asinghani/drive-by-wireless/experimental/pwm/Servo/pwm_servo.c

#include "pico/stdlib.h"
#include <stdio.h>
#include "hardware/pwm.h"
#include "hardware/clocks.h"

float clockDiv = 64;
float wrap = 39062;

void setMillis(int servoPin, float millis)
{
    pwm_set_gpio_level(servoPin, (millis/20000.f)*wrap);
}

void setServo(int servoPin, float startMillis)
{
    gpio_set_function(servoPin, GPIO_FUNC_PWM);
    uint slice_num = pwm_gpio_to_slice_num(servoPin);

    pwm_config config = pwm_get_default_config();
    
    uint64_t clockspeed = clock_get_hz(5);
    clockDiv = 64;
    wrap = 39062;

    while (clockspeed/clockDiv/50 > 65535 && clockDiv < 256) clockDiv += 64; 
    wrap = clockspeed/clockDiv/50;

    pwm_config_set_clkdiv(&config, clockDiv);
    pwm_config_set_wrap(&config, wrap);

    pwm_init(slice_num, &config, true);

    setMillis(servoPin, startMillis);
}

bool direction = true;
int currentMillis = 1385;       //gives centre point (actual angle is 90deg from left wheel)
int servoPin = 22;

int main()
{
    setServo(servoPin, currentMillis);
    while (true)
    {
        currentMillis += (direction)?5:-5;
        if (currentMillis >= 1685) direction = false;   //Right MAX from vehicles point of view
        if (currentMillis <= 1085) direction = true;    //Left MAX from vehicles point of view
        if (currentMillis <= 1085) direction = true;
        setMillis(servoPin, currentMillis);
        sleep_ms(10);
    }
}
