asinghani/drive-by-wireless/experimental/uwb_unit_test/deca_device.c

/*! ------------------------------------------------------------------------------------------------------------------
 * @file    deca_device.c
 * @brief   Decawave device configuration and control functions
 *
 * @attention
 *
 * Copyright 2013-2020 (c) Decawave Ltd, Dublin, Ireland.
 * Copyright 2021 (c) Callender-Consulting, LLC
 *
 * All rights reserved.
 *
 */

#include <assert.h>
#include <stdlib.h>
#include <stdint.h>
#include <stdio.h>
#include <string.h>

#include "deca_types.h"
#include "deca_regs.h"
#include "deca_device_api.h"
#include "deca_version.h"
#include "uwb_config.h"

#include "pico/stdlib.h"
#include "pico/binary_info.h"
#include "hardware/spi.h"

// -------------------------------------------------------------------------------------------------------------------
// Module Macro definitions and enumerations
//

#if 0
  #define DWT_API_ERROR_CHECK  /* API checks config input parameters */
#endif

/* STS Minimum Threshold (STS_MNTH) needs to be adjusted with changing STS length.
To adjust the STS_MNTH following formula can be used: STS_MNTH = SQRT(X/Y)*default_STS_MNTH
default_STS_MNTH is 0x10
X is the length of the STS in units of 8 (i.e. 8 for 64 length, 16 for 128 length etc.)
Y is either 8 or 16, 8 when no PDOA or PDOA mode 1 and 16 for PDOA mode 3

The API does not use the formula and the STS_MNTH value is derived from approximation formula as given by get_sts_mnth()
function. The API here supports STS lengths as listed in: dwt_sts_lengths_e enum, which are: 32, 64, 128, 256, 512, 1024, 2048
The enum value is used as the index into sts_length_factors array. The array has values which are generated by:
val = SQRT(stsLength/16)*2048
*/
const uint16_t sts_length_factors[STS_LEN_SUPPORTED]=
{
    1024,1448,2048,2896,4096,5793,8192
};

static uint16_t get_sts_mnth(uint16_t sts, uint8_t default_threshold, uint8_t shift_val);

//DW-IC SPI CRC-8 polynomial
#define POLYNOMIAL  0x07    /* x^8 + x^2 + x^1 + x^0 */
#define TOPBIT      (1 << (8 - 1))

// OTP addresses definitions
#define LDOTUNELO_ADDRESS (0x04)
#define LDOTUNEHI_ADDRESS (0x05)
#define PARTID_ADDRESS  (0x06)
#define LOTID_ADDRESS   (0x07)
#define VBAT_ADDRESS    (0x08)
#define VTEMP_ADDRESS   (0x09)
#define XTRIM_ADDRESS   (0x1E)
#define OTPREV_ADDRESS  (0x1F)
#define BIAS_TUNE_ADDRESS (0xA)
#define DGC_TUNE_ADDRESS (0x20)

// dwt_readcarrierintegrator defines
#define B20_SIGN_EXTEND_TEST (0x00100000UL)
#define B20_SIGN_EXTEND_MASK (0xFFF00000UL)
#define DRX_CARRIER_INT_LEN  (3)

#define CIA_MANUALLOWERBOUND_TH_64  (0x10) //cia lower bound threshold values for 64 MHz PRF
#define STSQUAL_THRESH_64 (0.90f)
 //STS quality threshold values for 64 MHz PRF
 //when using 64 MHz PRF the stsCpQual should be > 90 % of STS length

// dwt_readclockoffset defines
#define B11_SIGN_EXTEND_TEST (0x1000UL)
#define B11_SIGN_EXTEND_MASK (0xE000UL)

// dwt_readpdoa defines
#define B12_SIGN_EXTEND_TEST (0x2000UL)
#define B12_SIGN_EXTEND_MASK (0xC000UL)

// -------------------------------------------------------------------------------------------------------------------
// Macros and Enumerations for SPI & CLock blocks
//
#define DW3000_SPI_FAC      (0<<6 | 1<<0)
#define DW3000_SPI_FARW     (0<<6 | 0<<0)
#define DW3000_SPI_EAMRW    (1<<6)

// Defines for enable_clocks function
#define FORCE_CLK_SYS_TX        (1)
#define FORCE_CLK_AUTO          (5)
//SYSCLK
#define FORCE_SYSCLK_PLL        (2)
#define FORCE_SYSCLK_FOSCDIV4   (1)
#define FORCE_SYSCLK_FOSC       (3)
//RX and TX CLK
#define FORCE_CLK_PLL           (2)

#define SEL_CHANNEL5            (5)
#define SEL_CHANNEL9            (9)

// -------------------------------------------------------------------------------------------------------------------
// Internal functions prototypes for controlling and configuring the device
//
static void dwt_force_clocks(int clocks);
static uint32_t _dwt_otpread(uint16_t address);                     // Read non-volatile memory
static void _dwt_otpprogword32(uint32_t data, uint16_t address);  // Program the non-volatile memory

// -------------------------------------------------------------------------------------------------------------------
// Data for DW3000 Decawave Transceiver control
//
// Structure to hold the device data
typedef struct
{
    uint32_t      partID ;            // IC Part ID - read during initialisation
    uint32_t      lotID ;             // IC Lot ID - read during initialisation
    uint8_t       bias_tune;          // bias tune code
    uint8_t       dgc_otp_set;        // Flag to check if DGC values are programmed in OTP
    uint8_t       vBatP;              // IC V bat read during production and stored in OTP (Vmeas @ 3V3)
    uint8_t       tempP;              // IC temp read during production and stored in OTP (Tmeas @ 23C)
    uint8_t       longFrames ;        // Flag in non-standard long frame mode
    uint8_t       otprev ;            // OTP revision number (read during initialisation)
    uint8_t       init_xtrim;         // initial XTAL trim value read from OTP (or defaulted to mid-range if OTP not programmed)
    uint8_t       dblbuffon;          // Double RX buffer mode and DB status flag
    uint16_t      sleep_mode;         // Used for automatic reloading of LDO tune and microcode at wake-up
    int16_t       ststhreshold;       // Threshold for deciding if received STS is good or bad
    dwt_spi_crc_mode_e   spicrc;      // Use SPI CRC when this flag is true
    uint8_t       stsconfig;          // STS configuration mode
    uint8_t       cia_diagnostic;     // CIA dignostic logging level
    dwt_cb_data_t cbData;             // Callback data structure
    dwt_spierrcb_t cbSPIRDErr;        // Callback for SPI read error events
    dwt_cb_t    cbTxDone;             // Callback for TX confirmation event
    dwt_cb_t    cbRxOk;               // Callback for RX good frame event
    dwt_cb_t    cbRxTo;               // Callback for RX timeout events
    dwt_cb_t    cbRxErr;              // Callback for RX error events
    dwt_cb_t    cbSPIErr;             // Callback for SPI error events
    dwt_cb_t    cbSPIRdy;             // Callback for SPI ready events
} dwt_local_data_t ;


// -------------------------------------------------------------------------------------------------------------------
// Local variables
//
static dwt_local_data_t   DW3000local[DWT_NUM_DW_DEV] ; // Local device data, can be an array to support multiple DW3000 testing applications/platforms
static dwt_local_data_t *pdw3000local = &DW3000local[0];   // Local data structure pointer
static uint8_t crcTable[256];

/*! ------------------------------------------------------------------------------------------------------------------
 * @brief This function returns the version of the API as defined by DW3000_DRIVER_VERSION
 *
 * input parameters
 *
 * output parameters
 *
 * returns version (DW3000_DRIVER_VERSION)
 */
int32_t dwt_apiversion(void)
{
    return DW3000_DRIVER_VERSION;
}

/*! ------------------------------------------------------------------------------------------------------------------
 * @brief This function sets the local data structure pointer to point to the element in the local array as given by the index.
 *
 * input parameters
 * @param index    - selects the array element to point to. Must be within the array bounds, i.e. < DWT_NUM_DW_DEV
 *
 * output parameters
 *
 * returns DWT_SUCCESS for success, or DWT_ERROR for error
 */
int dwt_setlocaldataptr(unsigned int index)
{
    // Check the index is within the array bounds
    if (DWT_NUM_DW_DEV <= index) // return error if index outside the array bounds
    {
        return DWT_ERROR ;
    }

    pdw3000local = &DW3000local[index];

    return DWT_SUCCESS ;
}

/*! ------------------------------------------------------------------------------------------------------------------
* @brief  this function is used to read/write to the DW3000 device registers
*
* input parameters:
* @param recordNumber  - ID of register file or buffer being accessed
* @param index         - byte index into register file or buffer being accessed
* @param length        - number of bytes being written
* @param buffer        - pointer to buffer containing the 'length' bytes to be written
* @param rw            - DW3000_SPI_WR_BIT/DW3000_SPI_RD_BIT
*
* no return value
*/
static
void dwt_xfer3000
(
    const uint32_t    regFileID,  //0x0, 0x04-0x7F ; 0x10000, 0x10004, 0x10008-0x1007F; 0x20000 etc
    const uint16_t    indx,       //sub-index, calculated from regFileID 0..0x7F,
    const uint16_t    length,
    uint8_t           *buffer,
    const spi_modes_e mode
)
{
    uint8_t  header[2];           // Buffer to compose header in
    uint16_t cnt = 0;             // Counter for length of a header

    uint16_t reg_file     = 0x1F & ((regFileID + indx) >> 16);
    uint16_t reg_offset   = 0x7F &  (regFileID + indx);

    assert(reg_file     <= 0x1F);
    assert(reg_offset   <= 0x7F);
    assert(length       < 0x3100);
    assert(mode == DW3000_SPI_WR_BIT ||\
           mode == DW3000_SPI_RD_BIT ||\
           mode == DW3000_SPI_AND_OR_8 ||\
           mode == DW3000_SPI_AND_OR_16 ||\
           mode == DW3000_SPI_AND_OR_32);

    // Write message header selecting WRITE operation and addresses as appropriate
    uint16_t  addr;
    addr = (reg_file << 9) | (reg_offset << 2);

    header[0] = (uint8_t)((mode | addr) >> 8);//  & 0xFF; //bit7 + addr[4:0] + sub_addr[6:6]
    header[1] = (uint8_t)(addr | (mode & 0x03));// & 0xFF; //EAM: subaddr[5:0]+ R/W/AND_OR

    if (/*reg_offset == 0 && */length == 0)
    {   /* Fast Access Commands (FAC)
         * only write operation is possible for this mode
         * bit_7=one is W operation, bit_6=zero: FastAccess command, bit_[5..1] addr, bits_0=one: MODE of FastAccess
         */
        assert(mode == DW3000_SPI_WR_BIT);

        header[0] = (uint8_t)((DW3000_SPI_WR_BIT>>8) | (regFileID<<1) | DW3000_SPI_FAC);
        cnt = 1;
    }
    else if (reg_offset == 0 /*&& length > 0*/ && (mode == DW3000_SPI_WR_BIT || mode == DW3000_SPI_RD_BIT))
    {   /* Fast Access Commands with Read/Write support (FACRW)
         * bit_7 is R/W operation, bit_6=zero: FastAccess command, bit_[5..1] addr, bits_0=zero: MODE of FastAccess
         */
        header[0] |= DW3000_SPI_FARW;
        cnt = 1;
    }
    else
    {   /* Extended Address Mode with Read/Write support (EAMRW)
         * b[0] = bit_7 is R/W operation, bit_6 one = ExtendedAddressMode;
         * b[1] = addr<<2 | (mode&0x3)
         */
        header[0] |= DW3000_SPI_EAMRW;
        cnt = 2;
    }

    switch (mode)
    {
    case    DW3000_SPI_AND_OR_8:
    case    DW3000_SPI_AND_OR_16:
    case    DW3000_SPI_AND_OR_32:
    case    DW3000_SPI_WR_BIT:
    {
        uint8_t crc8 = 0;
        if (pdw3000local->spicrc != DWT_SPI_CRC_MODE_NO)
        {
            //generate 8 bit CRC
            crc8 = dwt_generatecrc8(header, cnt, 0);
            crc8 = dwt_generatecrc8(buffer, length, crc8);

            // Write it to the SPI
            writetospiwithcrc(cnt, header, length, buffer, crc8);
        }
        else
        {
            // Write it to the SPI
            writetospi(cnt, header, length, buffer);
        }
        break;
    }
    case DW3000_SPI_RD_BIT:
        {
            readfromspi(cnt, header, length, buffer);

            //check that the SPI read has correct CRC-8 byte
            //also don't do for SPICRC_CFG_ID register itself to prevent infinite recursion
            if ((pdw3000local->spicrc == DWT_SPI_CRC_MODE_WRRD) && (regFileID != SPICRC_CFG_ID))
            {
                uint8_t crc8, dwcrc8;
                //generate 8 bit CRC from the read data
                crc8 = dwt_generatecrc8(header, cnt, 0);
                crc8 = dwt_generatecrc8(buffer, length, crc8);

                //read the CRC that was generated in the DW3000 for the read transaction
                dwcrc8 = dwt_read8bitoffsetreg(SPICRC_CFG_ID, 0);

                //if the two CRC don't match report SPI read error
                //potential problem in callback if it will try to read/write SPI with CRC again.
                if (crc8 != dwcrc8)
                {
                    if (pdw3000local->cbSPIRDErr != NULL)
                        pdw3000local->cbSPIRDErr();
                }

            }
            break;
        }
    default:
        while(1);
        break;
    }

} // end dwt_xfer3000()

/*! ------------------------------------------------------------------------------------------------------------------
 * @brief  this function is used to write to the DW3000 device registers
 *
 * input parameters:
 * @param recordNumber  - ID of register file or buffer being accessed
 * @param index         - byte index into register file or buffer being accessed
 * @param length        - number of bytes being written
 * @param buffer        - pointer to buffer containing the 'length' bytes to be written
 *
 * output parameters
 *
 * no return value
 */
//static
void dwt_writetodevice
(
    uint32_t      regFileID,
    uint16_t      index,
    uint16_t      length,
    uint8_t       *buffer
)
{
    dwt_xfer3000(regFileID, index, length, buffer, DW3000_SPI_WR_BIT);
}

/*! ------------------------------------------------------------------------------------------------------------------
 * @brief  This function wakeup device by an IO pin. DW3000 SPI_CS or WAKEUP pins can be used for this.
 *         wakeup_device_with_io() which is external to this file and is platform dependant and it should be modified to
 *         toggle the correct pin depending on the HW/MCU connections with DW3000.
 *
 * @param None
 *
 * output parameters
 *
 * no return value
 */
void dwt_wakeup_ic(void)
{
    wakeup_device_with_io();
}

/*! ------------------------------------------------------------------------------------------------------------------
 * @brief  this function is used to read from the DW3000 device registers
 *
 * @param recordNumber  - ID of register file or buffer being accessed
 * @param index         - byte index into register file or buffer being accessed
 * @param length        - number of bytes being read
 * @param buffer        - pointer to buffer in which to return the read data.
 *
 * output parameters
 *
 * no return value
 */
//static
void dwt_readfromdevice
(
    uint32_t  regFileID,
    uint16_t  index,
    uint16_t  length,
    uint8_t   *buffer
)
{
    dwt_xfer3000(regFileID, index, length, buffer, DW3000_SPI_RD_BIT);
}

/*! ------------------------------------------------------------------------------------------------------------------
 * @brief  this function is used to read 32-bit value from the DW3000 device registers
 *
 * input parameters:
 * @param regFileID - ID of register file or buffer being accessed
 * @param regOffset - the index into register file or buffer being accessed
 *
 * output parameters
 *
 * returns 32 bit register value
 */
uint32_t dwt_read32bitoffsetreg(int regFileID, int regOffset)
{
    int     j ;
    uint32_t  regval = 0 ;
    uint8_t   buffer[4] ;

    dwt_readfromdevice(regFileID,regOffset,4,buffer); // Read 4 bytes (32-bits) register into buffer

    for (j = 3 ; j >= 0 ; j --)
    {
        regval = (regval << 8) + buffer[j] ;
    }

    return (regval);

} // end dwt_read32bitoffsetreg()

/*! ------------------------------------------------------------------------------------------------------------------
 * @brief  this function is used to read 16-bit value from the DW3000 device registers
 *
 * input parameters:
 * @param regFileID - ID of register file or buffer being accessed
 * @param regOffset - the index into register file or buffer being accessed
 *
 * output parameters
 *
 * returns 16 bit register value
 */
uint16_t dwt_read16bitoffsetreg(int regFileID,int regOffset)
{
    uint16_t  regval = 0 ;
    uint8_t   buffer[2] ;

    dwt_readfromdevice(regFileID,regOffset,2,buffer); // Read 2 bytes (16-bits) register into buffer

    regval = ((uint16_t)buffer[1] << 8) + buffer[0] ;
    return regval ;

} // end dwt_read16bitoffsetreg()

/*! ------------------------------------------------------------------------------------------------------------------
 * @brief  this function is used to read an 8-bit value from the DW3000 device registers
 *
 * input parameters:
 * @param regFileID - ID of register file or buffer being accessed
 * @param regOffset - the index into register file or buffer being accessed
 *
 * output parameters
 *
 * returns 8-bit register value
 */
uint8_t dwt_read8bitoffsetreg(int regFileID, int regOffset)
{
    uint8_t regval;

    dwt_readfromdevice(regFileID, regOffset, 1, &regval);

    return regval ;
}

/*! ------------------------------------------------------------------------------------------------------------------
 * @brief  this function is used to write 32-bit value to the DW3000 device registers
 *
 * input parameters:
 * @param regFileID - ID of register file or buffer being accessed
 * @param regOffset - the index into register file or buffer being accessed
 * @param regval    - the value to write
 *
 * output parameters
 *
 * no return value
 */
void dwt_write32bitoffsetreg(int regFileID, int regOffset, uint32_t regval)
{
    int     j ;
    uint8_t   buffer[4] ;

    for ( j = 0 ; j < 4 ; j++ )
    {
        buffer[j] = (uint8_t)regval;
        regval >>= 8 ;
    }

    dwt_writetodevice(regFileID,regOffset,4,buffer);
} // end dwt_write32bitoffsetreg()

/*! ------------------------------------------------------------------------------------------------------------------
 * @brief  this function is used to write 16-bit value to the DW3000 device registers
 *
 * input parameters:
 * @param regFileID - ID of register file or buffer being accessed
 * @param regOffset - the index into register file or buffer being accessed
 * @param regval    - the value to write
 *
 * output parameters
 *
 * no return value
 */
void dwt_write16bitoffsetreg(int regFileID, int regOffset, uint16_t regval)
{
    uint8_t   buffer[2] ;

    buffer[0] = (uint8_t)regval;
    buffer[1] = regval >> 8 ;

    dwt_writetodevice(regFileID,regOffset,2,buffer);
} // end dwt_write16bitoffsetreg()

/*! ------------------------------------------------------------------------------------------------------------------
 * @brief  this function is used to write an 8-bit value to the DW3000 device registers
 *
 * input parameters:
 * @param regFileID - ID of register file or buffer being accessed
 * @param regOffset - the index into register file or buffer being accessed
 * @param regval    - the value to write
 *
 * output parameters
 *
 * no return value
 */
void dwt_write8bitoffsetreg(int regFileID, int regOffset, uint8_t regval)
{
    //uint8_t   buf[1];
    //buf[0] = regval;
    dwt_writetodevice(regFileID, regOffset, 1, &regval);
}

/*! ------------------------------------------------------------------------------------------------------------------
 * @brief  this function is used to modify a 32-bit value to the DW3000 device registers
 *
 * input parameters:
 * @param regFileID :   ID of register file or buffer being accessed
 * @param regOffset :   the index into register file or buffer being accessed
 * @param regval_and:   the value to AND to register
 * @param regval_or :   the value to OR to register
 * @output          :   no return value
 */
void dwt_modify32bitoffsetreg(const int regFileID, const int regOffset, const uint32_t _and, const uint32_t _or)
{
    uint8_t buf[8];
    buf[0] = (uint8_t)_and;//       &0xFF;
    buf[1] = (uint8_t)(_and>>8);//  &0xFF;
    buf[2] = (uint8_t)(_and>>16);// &0xFF;
    buf[3] = (uint8_t)(_and>>24);// &0xFF;
    buf[4] = (uint8_t)_or;//        &0xFF;
    buf[5] = (uint8_t)(_or>>8);//   &0xFF;
    buf[6] = (uint8_t)(_or>>16);//  &0xFF;
    buf[7] = (uint8_t)(_or>>24);//  &0xFF;
    dwt_xfer3000(regFileID, regOffset, sizeof(buf), buf, DW3000_SPI_AND_OR_32);
}

/*! ------------------------------------------------------------------------------------------------------------------
 * @brief  this function is used to modify a 16-bit value to the DW3000 device registers
 *
 * input parameters:
 * @param regFileID :   ID of register file or buffer being accessed
 * @param regOffset :   the index into register file or buffer being accessed
 * @param regval_and:   the value to AND to register
 * @param regval_or :   the value to OR to register
 * @output          :   no return value
 */
void dwt_modify16bitoffsetreg(const int regFileID, const int regOffset, const uint16_t _and, const uint16_t _or)
{
    uint8_t buf[4];
    buf[0] = (uint8_t)_and;//       &0xFF;
    buf[1] = (uint8_t)(_and>>8);//  &0xFF;
    buf[2] = (uint8_t)_or;//        &0xFF;
    buf[3] = (uint8_t)(_or>>8);//   &0xFF;
    dwt_xfer3000(regFileID, regOffset, sizeof(buf), buf, DW3000_SPI_AND_OR_16);
}

/*! ------------------------------------------------------------------------------------------------------------------
 * @brief  this function is used to modify a 8-bit value to the DW3000 device registers
 *
 * input parameters:
 * @param regFileID :   ID of register file or buffer being accessed
 * @param regOffset :   the index into register file or buffer being accessed
 * @param regval_and:   the value to AND to register
 * @param regval_or :   the value to OR to register
 * @output          :   no return value
 */
void dwt_modify8bitoffsetreg(const int regFileID, const int regOffset, const uint8_t _and, const uint8_t _or)
{
    uint8_t buf[2];
    buf[0] = _and;
    buf[1] = _or;
    dwt_xfer3000(regFileID, regOffset, sizeof(buf),buf, DW3000_SPI_AND_OR_8);
}

static
void _dwt_crc8init(void)
{
    uint8_t  remainder;
    int dividend;

    /*
    * Compute the remainder of each possible dividend.
    */
    for (dividend = 0; dividend < 256; ++dividend)
    {
        /*
        * Start with the dividend followed by zeros.
        */
        remainder = dividend;

        /*
        * Perform modulo-2 division, a bit at a time.
        */
        for (uint8_t bit = 8; bit > 0; --bit)
        {
            /*
            * Try to divide the current data bit.
            */
            if (remainder & TOPBIT)
            {
                remainder = (remainder << 1) ^ POLYNOMIAL;
            }
            else
            {
                remainder = (remainder << 1);
            }
        }

        /*
        * Store the result into the table.
        */
        crcTable[dividend] = remainder;
    }

}   /* _dwt_crc8init() */

/*! ------------------------------------------------------------------------------------------------------------------
* @brief  this function is used to calculate 8-bit CRC, it uses 100000111 polynomial (i.e. P(x) = x^8+ x^2+ x^1+ x^0)
* this function has been optimized to use crcTable[] and calculate the CRC on byte by byte basis.
*
* input parameters:
* @param byteArray         - data to calculate CRC for
* @param len               - length of byteArray
* @param crcRemainderInit  - the remainder is the crc, also it is initially set to the initialisation value for CRC calculation
*
* output parameters
*
* returns 8-bit calculate CRC value
*/
uint8_t dwt_generatecrc8(const uint8_t* byteArray, int len, uint8_t crcRemainderInit)
{
    uint8_t data;
    int byte;

    /*
    * Divide the message by the polynomial, a byte at a time.
    */
    for (byte = 0; byte < len; ++byte)
    {
        data = byteArray[byte] ^ crcRemainderInit;
        crcRemainderInit = crcTable[data];// ^ (crcRemainderInit << 8);
    }

    /*
    * The final remainder is the CRC.
    */
    return(crcRemainderInit);
}

/*! ------------------------------------------------------------------------------------------------------------------
* @brief This is used to enable SPI CRC check in DW3000
*
* input parameters
* @param crc_mode - if set to DWT_SPI_CRC_MODE_WR then SPI CRC checking will be performed in DW3000 on each SPI write
*                   last byte of the SPI write transaction needs to be the 8-bit CRC, if it does not match
*                   the one calculated by DW3000 SPI CRC ERROR event will be set in the status register (SYS_STATUS_SPICRC)
*
* @param spireaderr_cb - this needs to contain the callback function pointer which will be called when SPI read error
*                        is detected (when the DW3000 generated CRC does not match the one calculated by  dwt_generatecrc8
*                        following the SPI read transaction)
*
* output parameters
*
* no return value
*/
void dwt_enablespicrccheck(dwt_spi_crc_mode_e crc_mode, dwt_spierrcb_t spireaderr_cb)
{
    if (crc_mode != DWT_SPI_CRC_MODE_NO) //enable CRC check in DW3000
    {
        dwt_or8bitoffsetreg(SYS_CFG_ID, 0, SYS_CFG_SPI_CRC_BIT_MASK);

        if (crc_mode == DWT_SPI_CRC_MODE_WRRD) //enable CRC generation on SPI read transaction which the DW3000 will store in SPICRC_CFG_ID register
        {
            pdw3000local->cbSPIRDErr = spireaderr_cb;
        }
        //initialise the crc calculation lookup table
        _dwt_crc8init();
    }
    else
    {
        dwt_and8bitoffsetreg(SYS_CFG_ID, 0, (uint8_t)~SYS_CFG_SPI_CRC_BIT_MASK);
    }
    pdw3000local->spicrc = crc_mode;
}

static
void _dwt_prog_ldo_and_bias_tune(void)
{
    dwt_or16bitoffsetreg(OTP_CFG_ID, 0, LDO_BIAS_KICK);
    dwt_and_or16bitoffsetreg(BIAS_CTRL_ID, 0, (uint16_t)~BIAS_CTRL_BIAS_MASK, pdw3000local->bias_tune);
}

/*! ------------------------------------------------------------------------------------------------------------------
* @brief This function is a static function used to 'kick' the desired operating parameter set (OPS) table upon wakeup from sleep.
*        It will load the required OPS table configuration based upon what OPS table was set to be used in dwt_configure().
*
* input parameters
*
* output parameters
*
* no return value
*/
static
void _dwt_kick_ops_table_on_wakeup(void)
{
    /* Restore OPS table config and kick. */
    /* Correct sleep mode should be set by dwt_configure() */

    /* Using the mask of all available OPS table options, check for OPS table options in the sleep mode mask */
    switch (pdw3000local->sleep_mode & (DWT_ALT_OPS | DWT_SEL_OPS0 | DWT_SEL_OPS1 | DWT_SEL_OPS2 | DWT_SEL_OPS3))
    {
    /* If preamble length >= 256 and set by dwt_configure(), the OPS table should be kicked off like so upon wakeup. */
    case (DWT_ALT_OPS | DWT_SEL_OPS0):
        dwt_modify32bitoffsetreg(OTP_CFG_ID, 0, ~(OTP_CFG_OPS_ID_BIT_MASK), DWT_OPSET_LONG | OTP_CFG_OPS_KICK_BIT_MASK);
        break;
    /* If SCP mode is enabled by dwt_configure(), the OPS table should be kicked off like so upon wakeup. */
    case (DWT_ALT_OPS | DWT_SEL_OPS1):
        dwt_modify32bitoffsetreg(OTP_CFG_ID, 0, ~(OTP_CFG_OPS_ID_BIT_MASK), DWT_OPSET_SCP | OTP_CFG_OPS_KICK_BIT_MASK);
        break;
    default:
        break;
    }
}

/*! ------------------------------------------------------------------------------------------------------------------
* @brief This function is a static function used to 'kick' the DGC upon wakeup from sleep. It will load the
*        required DGC configuration from OTP based upon what channel was set to be used in dwt_configure().
*
* input parameters
* @param channel - specifies the operating channel (e.g. 5 or 9)
*
* output parameters
*
* no return value
*/
static
void _dwt_kick_dgc_on_wakeup(int8_t channel)
{
    /* The DGC_SEL bit must be set to '0' for channel 5 and '1' for channel 9 */
    if (channel == 5)
    {
        dwt_modify32bitoffsetreg(OTP_CFG_ID, 0, ~(OTP_CFG_DGC_SEL_BIT_MASK),
                (DWT_DGC_SEL_CH5 << OTP_CFG_DGC_SEL_BIT_OFFSET) | OTP_CFG_DGC_KICK_BIT_MASK);
    }
    else if (channel == 9)
    {
        dwt_modify32bitoffsetreg(OTP_CFG_ID, 0, ~(OTP_CFG_DGC_SEL_BIT_MASK),
                (DWT_DGC_SEL_CH9 << OTP_CFG_DGC_SEL_BIT_OFFSET) | OTP_CFG_DGC_KICK_BIT_MASK);
    }
}

/*! ------------------------------------------------------------------------------------------------------------------
 * @brief This function initialises the DW3000 transceiver:
 * it reads its DEV_ID register (address 0x00) to verify the IC is one supported
 * by this software (e.g. DW3000 32-bit device ID value is 0xDECA03xx).  Then it
 * does any initial once only device configurations needed for use and initialises
 * as necessary any static data items belonging to this low-level driver.
 *
 * NOTES:
 * 1.it also reads and applies LDO and BIAS tune and crystal trim values from OTP memory
 * 2.it is assumed this function is called after a reset or on power up of the DW3000
 *
 * input parameters
 * @param mode - mask which defines which OTP values to read.
 *
 * output parameters
 *
 * returns DWT_SUCCESS for success, or DWT_ERROR for error
 */
int dwt_initialise(int mode)
{
   //uint16_t otp_addr;
   //uint32_t devid;
    uint32_t ldo_tune_lo;
    uint32_t ldo_tune_hi;

    pdw3000local->dblbuffon = DBL_BUFF_OFF; // Double buffer mode off by default / clear the flag
    pdw3000local->sleep_mode = DWT_RUNSAR;  // Configure RUN_SAR on wake by default as it is needed when running PGF_CAL
    pdw3000local->spicrc = 0;
    pdw3000local->stsconfig = 0; //STS off
    pdw3000local->vBatP = 0;
    pdw3000local->tempP = 0;

    pdw3000local->cbTxDone = NULL;
    pdw3000local->cbRxOk = NULL;
    pdw3000local->cbRxTo = NULL;
    pdw3000local->cbRxErr = NULL;
    pdw3000local->cbSPIRdy = NULL;
    pdw3000local->cbSPIErr = NULL;

    // Read and validate device ID return -1 if not recognised
    if (dwt_check_dev_id()!=DWT_SUCCESS)
    {
        return DWT_ERROR;
    }

    //Read LDO_TUNE and BIAS_TUNE from OTP
    ldo_tune_lo = _dwt_otpread(LDOTUNELO_ADDRESS);
    ldo_tune_hi = _dwt_otpread(LDOTUNEHI_ADDRESS);
    pdw3000local->bias_tune = (_dwt_otpread(BIAS_TUNE_ADDRESS) >> 16) & BIAS_CTRL_BIAS_MASK;

    if ((ldo_tune_lo != 0) && (ldo_tune_hi != 0) && (pdw3000local->bias_tune != 0))
    {
        _dwt_prog_ldo_and_bias_tune();
    }

    // Read DGC_CFG from OTP
    if (_dwt_otpread(DGC_TUNE_ADDRESS) == DWT_DGC_CFG0)
    {
        pdw3000local->dgc_otp_set = DWT_DGC_LOAD_FROM_OTP;
    }
    else
    {
        pdw3000local->dgc_otp_set = DWT_DGC_LOAD_FROM_SW;
    }

    // Load Part and Lot ID from OTP
    if(mode & DWT_READ_OTP_PID)
        pdw3000local->partID = _dwt_otpread(PARTID_ADDRESS);
    if (mode & DWT_READ_OTP_LID)
        pdw3000local->lotID = _dwt_otpread(LOTID_ADDRESS);
    if (mode & DWT_READ_OTP_BAT)
        pdw3000local->vBatP = (uint8_t)_dwt_otpread(VBAT_ADDRESS);
    if (mode & DWT_READ_OTP_TMP)
        pdw3000local->tempP = (uint8_t)_dwt_otpread(VTEMP_ADDRESS);


    if(pdw3000local->tempP == 0) //if the reference temperature has not been programmed in OTP (early eng samples) set to default value
    {
        pdw3000local->tempP = 0x85 ; //@temp of 20 deg
    }

    if(pdw3000local->vBatP == 0) //if the reference voltage has not been programmed in OTP (early eng samples) set to default value
    {
        pdw3000local->vBatP = 0x74 ;  //@Vref of 3.0V
    }

    pdw3000local->otprev = (uint8_t) _dwt_otpread(OTPREV_ADDRESS);

    pdw3000local->init_xtrim = _dwt_otpread(XTRIM_ADDRESS) & 0x7f;
    if(pdw3000local->init_xtrim == 0)
    {
        pdw3000local->init_xtrim = 0x2E ; //set default value
    }
    dwt_write8bitoffsetreg(XTAL_ID, 0, pdw3000local->init_xtrim);


    return DWT_SUCCESS ;

} // end dwt_initialise()

/*! ------------------------------------------------------------------------------------------------------------------
 * @brief This function can place DW3000 into IDLE/IDLE_PLL or IDLE_RC mode when it is not actively in TX or RX.
 *
 * input parameters
 * @param state - DWT_DW_IDLE (1) to put DW3000 into IDLE/IDLE_PLL state; DWT_DW_INIT (0) to put DW3000 into INIT_RC state;
 *                DWT_DW_IDLE_RC (2) to put DW3000 into IDLE_RC state.
 *
 * output parameters none
 *
 * no return value
 */
void dwt_setdwstate(int state)
{
    if (state == DWT_DW_IDLE) // Set the auto INIT2IDLE bit so that DW3000 enters IDLE mode before switching clocks to system_PLL
    //NOTE: PLL should be configured prior to this, and the device should be in IDLE_RC (if the PLL does not lock device will remain in IDLE_RC)
    {
        //switch clock to auto - if coming here from INIT_RC the clock will be FOSC/4, need to switch to auto prior to setting auto INIT2IDLE bit
        dwt_force_clocks(FORCE_CLK_AUTO);
        dwt_or8bitoffsetreg(SEQ_CTRL_ID, 0x01, SEQ_CTRL_AINIT2IDLE_BIT_MASK>>8);
    }
    else if(state == DWT_DW_IDLE_RC)  //Change state to IDLE_RC and clear auto INIT2IDLE bit
    {
        //switch clock to FOSC
        dwt_or8bitoffsetreg(CLK_CTRL_ID, 0, FORCE_SYSCLK_FOSC);
        //clear the auto INIT2IDLE bit and set FORCE2INIT
        dwt_modify32bitoffsetreg(SEQ_CTRL_ID, 0x0, (uint32_t) ~SEQ_CTRL_AINIT2IDLE_BIT_MASK, SEQ_CTRL_FORCE2INIT_BIT_MASK);
        //clear force bits (device will stay in IDLE_RC)
        dwt_and8bitoffsetreg(SEQ_CTRL_ID, 0x2, (uint8_t) ~(SEQ_CTRL_FORCE2INIT_BIT_MASK>>16));
        //switch clock to auto
        dwt_force_clocks(FORCE_CLK_AUTO);
    }
    else
    //NOTE: the SPI rate needs to be <= 7MHz as device is switching to INIT_RC state
    {
        dwt_or8bitoffsetreg(CLK_CTRL_ID, 0, FORCE_SYSCLK_FOSCDIV4);
        //clear the auto INIT2IDLE bit and set FORCE2INIT
        dwt_modify32bitoffsetreg(SEQ_CTRL_ID, 0x0, (uint32_t) ~SEQ_CTRL_AINIT2IDLE_BIT_MASK, SEQ_CTRL_FORCE2INIT_BIT_MASK);
        dwt_and8bitoffsetreg(SEQ_CTRL_ID, 0x2, (uint8_t) ~(SEQ_CTRL_FORCE2INIT_BIT_MASK>>16));
    }
}

/*! ------------------------------------------------------------------------------------------------------------------
 * @brief This is used to enable GPIO clocks. The clocks are needed to ensure correct GPIO operation
 *
 * input parameters
 *
 * output parameters
 *
 * no return value
 */
void dwt_enablegpioclocks(void)
{
    dwt_or32bitoffsetreg(CLK_CTRL_ID, 0, CLK_CTRL_GPIO_CLK_EN_BIT_MASK);
}

/*! ------------------------------------------------------------------------------------------------------------------
 * @brief This is used to return the read OTP revision
 *
 * NOTE: dwt_initialise() must be called prior to this function so that it can return a relevant value.
 *
 * input parameters
 *
 * output parameters
 *
 * returns the read OTP revision value
 */
uint8_t dwt_otprevision(void)
{
    return pdw3000local->otprev ;
}

/*! ------------------------------------------------------------------------------------------------------------------
 * @brief This function enables/disables the fine grain TX sequencing (this is enabled by default in the DW3000).
 *
 * input parameters
 * @param enable - 1 to enable fine grain TX sequencing, 0 to disable it.
 *
 * output parameters none
 *
 * no return value
 */
void dwt_setfinegraintxseq(int enable)
{
    if (enable)
    {
        dwt_write32bitoffsetreg(PWR_UP_TIMES_LO_ID, 2, PMSC_TXFINESEQ_ENABLE);
    }
    else
    {
        dwt_write32bitoffsetreg(PWR_UP_TIMES_LO_ID, 2, PMSC_TXFINESEQ_DISABLE);
    }
}

/*! ------------------------------------------------------------------------------------------------------------------
 * @brief This is used to enable GPIO for external LNA or PA functionality - HW dependent, consult the DW3000 User Manual.
 *        This can also be used for debug as enabling TX and RX GPIOs is quite handy to monitor DW3000's activity.
 *
 * NOTE: Enabling PA functionality requires that fine grain TX sequencing is deactivated. This can be done using
 *       dwt_setfinegraintxseq().
 *
 * input parameters
 * @param lna_pa - bit field: bit 0 if set will enable LNA functionality,
 *                          : bit 1 if set will enable PA functionality,
 *                          : to disable LNA/PA set the bits to 0
 * output parameters
 *
 * no return value
 */
void dwt_setlnapamode(int lna_pa)
{
    uint32_t gpio_mode = dwt_read32bitreg(GPIO_MODE_ID);
    gpio_mode &= (~(GPIO_MODE_MSGP0_MODE_BIT_MASK | GPIO_MODE_MSGP1_MODE_BIT_MASK
            | GPIO_MODE_MSGP4_MODE_BIT_MASK | GPIO_MODE_MSGP5_MODE_BIT_MASK | GPIO_MODE_MSGP6_MODE_BIT_MASK)); //clear GPIO 4, 5, 6, configuration
    if (lna_pa & DWT_LNA_ENABLE)
    {
        gpio_mode |= GPIO_PIN6_EXTRX;
    }
    if (lna_pa & DWT_PA_ENABLE)
    {
        gpio_mode |= (GPIO_PIN4_EXTDA | GPIO_PIN5_EXTTX);
    }
    if (lna_pa & DWT_TXRX_EN)
    {
        gpio_mode |= (GPIO_PIN0_EXTTXE | GPIO_PIN1_EXTRXE);
    }

    dwt_write32bitreg(GPIO_MODE_ID, gpio_mode);
}

/*! ------------------------------------------------------------------------------------------------------------------
 * @brief Returns the PG delay value of the TX
 *
 * input parameters
 *
 * output parameters
 *
 * returns uint8_t
 */
uint8_t dwt_readpgdelay(void)
{
    return dwt_read8bitoffsetreg(TX_CTRL_HI_ID, 0);
}

/*! ------------------------------------------------------------------------------------------------------------------
 * @brief This is used to return the read V measured @ 3.3 V value recorded in OTP address 0x8 (VBAT_ADDRESS)
 *
 * NOTE: dwt_initialise() must be called prior to this function so that it can return a relevant value.
 *
 * input parameters
 *
 * output parameters
 *
 * returns the 8 bit V bat value as programmed in the factory
 */
uint8_t dwt_geticrefvolt(void)
{
    return pdw3000local->vBatP;
}

/*! ------------------------------------------------------------------------------------------------------------------
* @brief This is used to return the read T measured @ 23 C value recorded in OTP address 0x9 (VTEMP_ADDRESS)
*
* NOTE: dwt_initialise() must be called prior to this function so that it can return a relevant value.
*
* input parameters
*
* output parameters
*
* returns the 8 bit V temp value as programmed in the factory
*/
uint8_t dwt_geticreftemp(void)
{
    return pdw3000local->tempP;
}

/*! ------------------------------------------------------------------------------------------------------------------
 * @brief This is used to return the read part ID of the device
 *
 * NOTE: dwt_initialise() must be called prior to this function so that it can return a relevant value.
 *
 * input parameters
 *
 * output parameters
 *
 * returns the 32 bit part ID value as programmed in the factory
 */
uint32_t dwt_getpartid(void)
{
    return pdw3000local->partID;
}

/*! ------------------------------------------------------------------------------------------------------------------
 * @brief This is used to return the read lot ID of the device
 *
 * NOTE: dwt_initialise() must be called prior to this function so that it can return a relevant value.
 *
 * input parameters
 *
 * output parameters
 *
 * returns the 32 bit lot ID value as programmed in the factory
 */
uint32_t dwt_getlotid(void)
{
    return pdw3000local->lotID;
}

/*! ------------------------------------------------------------------------------------------------------------------
 * @brief This is used to return the read device type and revision information of the DW3000 device (MP part is 0xDECA0300)
 *
 * input parameters
 *
 * output parameters
 *
 * returns the read value which for DW3000 is 0xDECA0312/0xDECA0302
 */
uint32_t dwt_readdevid(void)
{
    return dwt_read32bitoffsetreg(DEV_ID_ID, 0);
}

/*! ------------------------------------------------------------------------------------------------------------------
 * @brief This function provides the API for the configuration of the TX spectrum
 * including the power and pulse generator delay. The input is a pointer to the data structure
 * of type dwt_txconfig_t that holds all the configurable items.
 *
 * input parameters
 * @param config    -   pointer to the txrf configuration structure, which contains the tx rf config data
 *                      If config->PGcount == 0 the PGdelay value will be used, else the PG calibration will run
 *
 * output parameters
 *
 * no return value
 */
void dwt_configuretxrf(dwt_txconfig_t *config)
{
    if (config->PGcount == 0) {
        // Configure RF TX PG_DELAY
        dwt_write8bitoffsetreg(TX_CTRL_HI_ID, 0, config->PGdly);
    }
    else
    {
        uint8_t channel = 5;
        if (dwt_read8bitoffsetreg(CHAN_CTRL_ID, 0) & 0x1)
        {
            channel = 9;
        }
        dwt_calcbandwidthadj(config->PGcount, channel);
    }

    // Configure TX power
    dwt_write32bitreg(TX_POWER_ID, config->power);
}

/*! ------------------------------------------------------------------------------------------------------------------
 * @brief This function configures the STS AES 128 bit key value.
 * the default value is [31:00]c9a375fa,
 *                      [63:32]8df43a20,
 *                      [95:64]b5e5a4ed,
 *                     [127:96]0738123b
 *
 * input parameters
 * @param pStsKey - the pointer to the structure of dwt_sts_cp_key_t type, which holds the AES128 key value to generate STS
 *
 * output parameters
 *
 * no return value
 */
void dwt_configurestskey(dwt_sts_cp_key_t* pStsKey)
{
    dwt_write32bitreg(STS_KEY0_ID, pStsKey->key0);
    dwt_write32bitreg(STS_KEY1_ID, pStsKey->key1);
    dwt_write32bitreg(STS_KEY2_ID, pStsKey->key2);
    dwt_write32bitreg(STS_KEY3_ID, pStsKey->key3);
}

/*! ------------------------------------------------------------------------------------------------------------------
 * @brief This function configures the STS AES 128 bit initial value, the default value is 1, i.e. DW3000 reset value is 1.
 *
 * input parameters
 * @param pStsIv - the pointer to the structure of dwt_sts_cp_iv_t type, which holds the IV value to generate STS
 *
 * output parameters
 *
 * no return value
 */
void dwt_configurestsiv(dwt_sts_cp_iv_t* pStsIv)
{
    dwt_write32bitreg(STS_IV0_ID, pStsIv->iv0);
    dwt_write32bitreg(STS_IV1_ID, pStsIv->iv1);
    dwt_write32bitreg(STS_IV2_ID, pStsIv->iv2);
    dwt_write32bitreg(STS_IV3_ID, pStsIv->iv3);
}

/*! ------------------------------------------------------------------------------------------------------------------
 * @brief This function re-loads the STS initial value
 *
 * input parameters
 *
 * output parameters
 *
 * no return value
 */
void dwt_configurestsloadiv(void)
{
    dwt_or8bitoffsetreg(STS_CTRL_ID, 0, STS_CTRL_LOAD_IV_BIT_MASK);
}

static
uint16_t get_sts_mnth (uint16_t cipher, uint8_t threshold, uint8_t shift_val)
{
    uint32_t  value;
    uint16_t  mod_val;

    value = cipher* (uint32_t)threshold;
    if (shift_val == 3)
    {
        value *= SQRT_FACTOR;//Factor to sqrt(2)
        value >>= SQRT_SHIFT_VAL;
    }

    mod_val = value % MOD_VALUE+ HALF_MOD;
    value >>= SHIFT_VALUE;
    /* Check if modulo greater than MOD_VALUE, if yes add 1 */
    if (mod_val >= MOD_VALUE)
        value += 1;

    return (uint16_t)value;
}

/*! ------------------------------------------------------------------------------------------------------------------
 * @brief This function sets the default values of the lookup tables depending on the channel selected.
 *
 * input parameters
 * @param[in] channel - Channel that the device will be transmitting/receiving on.
 *
 * no return value
 */
void dwt_configmrxlut(int channel)
{
	uint32_t lut0, lut1, lut2, lut3, lut4, lut5, lut6 = 0;

    if (channel == 5)
    {
        lut0 = (uint32_t)CH5_DGC_LUT_0;
        lut1 = (uint32_t)CH5_DGC_LUT_1;
        lut2 = (uint32_t)CH5_DGC_LUT_2;
        lut3 = (uint32_t)CH5_DGC_LUT_3;
        lut4 = (uint32_t)CH5_DGC_LUT_4;
        lut5 = (uint32_t)CH5_DGC_LUT_5;
        lut6 = (uint32_t)CH5_DGC_LUT_6;
    }
    else
    {
        lut0 = (uint32_t)CH9_DGC_LUT_0;
        lut1 = (uint32_t)CH9_DGC_LUT_1;
        lut2 = (uint32_t)CH9_DGC_LUT_2;
        lut3 = (uint32_t)CH9_DGC_LUT_3;
        lut4 = (uint32_t)CH9_DGC_LUT_4;
        lut5 = (uint32_t)CH9_DGC_LUT_5;
        lut6 = (uint32_t)CH9_DGC_LUT_6;
    }
    dwt_write32bitoffsetreg(DGC_LUT_0_CFG_ID, 0x0, lut0);
    dwt_write32bitoffsetreg(DGC_LUT_1_CFG_ID, 0x0, lut1);
    dwt_write32bitoffsetreg(DGC_LUT_2_CFG_ID, 0x0, lut2);
    dwt_write32bitoffsetreg(DGC_LUT_3_CFG_ID, 0x0, lut3);
    dwt_write32bitoffsetreg(DGC_LUT_4_CFG_ID, 0x0, lut4);
    dwt_write32bitoffsetreg(DGC_LUT_5_CFG_ID, 0x0, lut5);
    dwt_write32bitoffsetreg(DGC_LUT_6_CFG_ID, 0x0, lut6);
    dwt_write32bitoffsetreg(DGC_CFG0_ID, 0x0, DWT_DGC_CFG0);
    dwt_write32bitoffsetreg(DGC_CFG1_ID, 0x0, DWT_DGC_CFG1);
}

/*! ------------------------------------------------------------------------------------------------------------------
 * @brief This function needs to be called after device is woken up from DEEPSLEEP/SLEEP state, to restore the
 * configuration which has not been automatically restored from AON
 *
 * input parameters
 *
 * return DWT_SUCCESS
 *
 */
void dwt_restoreconfig(void)
{
    uint8_t channel = 5;
    uint16_t chan_ctrl;

    if (pdw3000local->bias_tune != 0)
    {
        _dwt_prog_ldo_and_bias_tune();
    }
    dwt_write8bitoffsetreg(LDO_RLOAD_ID, 1, LDO_RLOAD_VAL_B1);
    /*Restoring indirect access register B configuration as this is not preserved when device is in DEEPSLEEP/SLEEP state.
     * Indirect access register B is configured to point to the "Double buffer diagnostic SET 2"*/
    dwt_write32bitreg(INDIRECT_ADDR_B_ID, (BUF1_RX_FINFO >> 16));
    dwt_write32bitreg(ADDR_OFFSET_B_ID, BUF1_RX_FINFO & 0xffff);

    /* Restore OPS table configuration */
    _dwt_kick_ops_table_on_wakeup();

    chan_ctrl = dwt_read16bitoffsetreg(CHAN_CTRL_ID, 0);

    //assume RX code is the same as TX (e.g. we will not RX on 16 MHz or SCP and TX on 64 MHz)
    if( (((chan_ctrl>> CHAN_CTRL_TX_PCODE_BIT_OFFSET)&CHAN_CTRL_TX_PCODE_BIT_MASK) >= 9) && (((chan_ctrl >> CHAN_CTRL_TX_PCODE_BIT_OFFSET)&CHAN_CTRL_TX_PCODE_BIT_MASK) <= 24)) //only enable DGC for PRF 64
    {
        if (chan_ctrl & 0x1)
        {
            channel = 9;
        }

        /* If the OTP has DGC info programmed into it, do a manual kick from OTP. */
        if (pdw3000local->dgc_otp_set == DWT_DGC_LOAD_FROM_OTP)
        {
            _dwt_kick_dgc_on_wakeup(channel);
        }
        /* Else we manually program hard-coded values into the DGC registers. */
        else
        {
            dwt_configmrxlut(channel);
        }
    }
}

/*! ------------------------------------------------------------------------------------------------------------------
 * @brief This function configures STS mode: e.g. DWT_STS_MODE_OFF, DWT_STS_MODE_1 etc
 * The dwt_configure should be called prior to this to configure other parameters
 *
 * input parameters
 * @param stsMode    -   e.g. DWT_STS_MODE_OFF, DWT_STS_MODE_1 etc.
 *
 * return DWT_SUCCESS
 *
 */
void dwt_configurestsmode(uint8_t stsMode)
{

    pdw3000local->stsconfig = stsMode;

    /////////////////////////////////////////////////////////////////////////
    //SYS_CFG
    //clear the PHR Mode, PHR Rate, STS Protocol, SDC, PDOA Mode,
    //then set the relevant bits according to configuration of the PHR Mode, PHR Rate, STS Protocol, SDC, PDOA Mode,
    dwt_modify32bitoffsetreg(SYS_CFG_ID, 0, ~(SYS_CFG_CP_SPC_BIT_MASK | SYS_CFG_CP_SDC_BIT_MASK),
        ((uint16_t)stsMode & DWT_STS_CONFIG_MASK) << SYS_CFG_CP_SPC_BIT_OFFSET);

    if((stsMode & DWT_STS_MODE_ND) == DWT_STS_MODE_ND)
    {
        //configure lower preamble detection threshold for no data STS mode
        dwt_write32bitoffsetreg(DTUNE3_ID, 0, PD_THRESH_NO_DATA);
    }
    else
    {
        dwt_write32bitoffsetreg(DTUNE3_ID, 0, PD_THRESH_DEFAULT);
    }
}

/*! ------------------------------------------------------------------------------------------------------------------
 * @brief This function provides the main API for the configuration of the
 * DW3000 and this low-level driver.  The input is a pointer to the data structure
 * of type dwt_config_t that holds all the configurable items.
 * The dwt_config_t structure shows which ones are supported
 *
 * input parameters
 * @param config    -   pointer to the configuration structure, which contains the device configuration data.
 *
 * return DWT_SUCCESS or DWT_ERROR
 * Note: If the RX calibration routine fails the device receiver performance will be severely affected,
 * the application should reset device and try again
 *
 */
int dwt_configure(dwt_config_t *config)
{
    uint8_t chan = config->chan,cnt,flag;
    uint32_t temp;
    uint8_t scp = ((config->rxCode > 24) || (config->txCode > 24)) ? 1 : 0;
    uint8_t mode = (config->phrMode == DWT_PHRMODE_EXT) ? SYS_CFG_PHR_MODE_BIT_MASK : 0;
    uint16_t sts_len;
    int error = DWT_SUCCESS;


#ifdef DWT_API_ERROR_CHECK
    assert((config->dataRate == DWT_BR_6M8) || (config->dataRate == DWT_BR_850K));
    assert(config->rxPAC <= DWT_PAC4);
    assert((chan == 5) || (chan == 9));
    assert((config->txPreambLength == DWT_PLEN_32)
           || (config->txPreambLength == DWT_PLEN_64)
           || (config->txPreambLength == DWT_PLEN_72)
           || (config->txPreambLength == DWT_PLEN_128)
           || (config->txPreambLength == DWT_PLEN_256)
           || (config->txPreambLength == DWT_PLEN_512)
           || (config->txPreambLength == DWT_PLEN_1024)
           || (config->txPreambLength == DWT_PLEN_1536)
           || (config->txPreambLength == DWT_PLEN_2048)
           || (config->txPreambLength == DWT_PLEN_4096));
    assert((config->phrMode == DWT_PHRMODE_STD)
           || (config->phrMode == DWT_PHRMODE_EXT));
    assert((config->phrRate == DWT_PHRRATE_STD)
           || (config->phrRate == DWT_PHRRATE_DTA));
    assert((config->pdoaMode == DWT_PDOA_M0)
           || (config->pdoaMode == DWT_PDOA_M1)
           || (config->pdoaMode == DWT_PDOA_M3));
    assert(((config->stsMode & DWT_STS_CONFIG_MASK) == DWT_STS_MODE_OFF)
           || ((config->stsMode & DWT_STS_CONFIG_MASK) == DWT_STS_MODE_1)
           || ((config->stsMode & DWT_STS_CONFIG_MASK) == DWT_STS_MODE_2)
           || ((config->stsMode & DWT_STS_CONFIG_MASK) == DWT_STS_MODE_ND)
           || ((config->stsMode & DWT_STS_CONFIG_MASK) == DWT_STS_MODE_SDC)
           || ((config->stsMode & DWT_STS_CONFIG_MASK) == (DWT_STS_MODE_1 | DWT_STS_MODE_SDC))
           || ((config->stsMode & DWT_STS_CONFIG_MASK) == (DWT_STS_MODE_2 | DWT_STS_MODE_SDC))
           || ((config->stsMode & DWT_STS_CONFIG_MASK) == (DWT_STS_MODE_ND | DWT_STS_MODE_SDC))
           || ((config->stsMode & DWT_STS_CONFIG_MASK) == DWT_STS_CONFIG_MASK));
#endif
    int preamble_len;

    switch (config->txPreambLength)
    {
    case DWT_PLEN_32:
        preamble_len = 32;
        break;
    case DWT_PLEN_64:
        preamble_len = 64;
        break;
    case DWT_PLEN_72:
        preamble_len = 72;
        break;
    case DWT_PLEN_128:
        preamble_len = 128;
        break;
    default:
        preamble_len = 256;
        break;
    }

    pdw3000local->sleep_mode &= (~(DWT_ALT_OPS | DWT_SEL_OPS3));  //clear the sleep mode ALT_OPS bit
    pdw3000local->longFrames = config->phrMode ;
    sts_len=GET_STS_REG_SET_VALUE((uint16_t)(config->stsLength));
    pdw3000local->ststhreshold = (int16_t)((((uint32_t)sts_len) * 8) * STSQUAL_THRESH_64);
    pdw3000local->stsconfig = config->stsMode;

    /////////////////////////////////////////////////////////////////////////
    //SYS_CFG
    //clear the PHR Mode, PHR Rate, STS Protocol, SDC, PDOA Mode,
    //then set the relevant bits according to configuration of the PHR Mode, PHR Rate, STS Protocol, SDC, PDOA Mode,
    dwt_modify32bitoffsetreg(SYS_CFG_ID, 0, ~(SYS_CFG_PHR_MODE_BIT_MASK  |
                                              SYS_CFG_PHR_6M8_BIT_MASK   |
                                              SYS_CFG_CP_SPC_BIT_MASK    |
                                              SYS_CFG_PDOA_MODE_BIT_MASK |
                                              SYS_CFG_CP_SDC_BIT_MASK),
        ((uint32_t)config->pdoaMode) << SYS_CFG_PDOA_MODE_BIT_OFFSET
        | ((uint16_t)config->stsMode & DWT_STS_CONFIG_MASK) << SYS_CFG_CP_SPC_BIT_OFFSET
        | (SYS_CFG_PHR_6M8_BIT_MASK & ((uint32_t)config->phrRate << SYS_CFG_PHR_6M8_BIT_OFFSET))
        | mode);


    if (scp)
    {
        //configure OPS tables for SCP mode
        pdw3000local->sleep_mode |= DWT_ALT_OPS | DWT_SEL_OPS1;  //configure correct OPS table is kicked on wakeup
        dwt_modify32bitoffsetreg(OTP_CFG_ID, 0, ~(OTP_CFG_OPS_ID_BIT_MASK), DWT_OPSET_SCP | OTP_CFG_OPS_KICK_BIT_MASK);

        dwt_write32bitoffsetreg(IP_CONFIG_LO_ID, 0, IP_CONFIG_LO_SCP);       //Set this if Ipatov analysis is used in SCP mode
        dwt_write32bitoffsetreg(IP_CONFIG_HI_ID, 0, IP_CONFIG_HI_SCP);

        dwt_write32bitoffsetreg(STS_CONFIG_LO_ID, 0, STS_CONFIG_LO_SCP);
        dwt_write8bitoffsetreg(STS_CONFIG_HI_ID, 0, STS_CONFIG_HI_SCP);
    }
    else //
    {
        uint16_t sts_mnth;
        if (config->stsMode != DWT_STS_MODE_OFF)
        {

            //configure CIA STS lower bound
            if ((config->pdoaMode == DWT_PDOA_M1) || (config->pdoaMode == DWT_PDOA_M0))
            {
                //In PDOA mode 1, number of accumulated symbols is the whole length of the STS
                sts_mnth=get_sts_mnth(sts_length_factors[(uint8_t)(config->stsLength)], CIA_MANUALLOWERBOUND_TH_64, 3);
            }
            else
            {
                //In PDOA mode 3 number of accumulated symbols is half of the length of STS symbols
                sts_mnth=get_sts_mnth(sts_length_factors[(uint8_t)(config->stsLength)], CIA_MANUALLOWERBOUND_TH_64, 4);
            }

            preamble_len += (sts_len) * 8;

            dwt_modify16bitoffsetreg(STS_CONFIG_LO_ID, 2, (uint16_t)~(STS_CONFIG_LO_STS_MAN_TH_BIT_MASK >> 16), sts_mnth & 0x7F);

        }

        //configure OPS tables for non-SCP mode
        if (preamble_len >= 256)
        {
            pdw3000local->sleep_mode |= DWT_ALT_OPS | DWT_SEL_OPS0;
            dwt_modify32bitoffsetreg(OTP_CFG_ID, 0, ~(OTP_CFG_OPS_ID_BIT_MASK), DWT_OPSET_LONG | OTP_CFG_OPS_KICK_BIT_MASK);
        }
        else
        {
            dwt_modify32bitoffsetreg(OTP_CFG_ID, 0, ~(OTP_CFG_OPS_ID_BIT_MASK), DWT_OPSET_SHORT | OTP_CFG_OPS_KICK_BIT_MASK);
        }

    }

    dwt_modify8bitoffsetreg(DTUNE0_ID, 0, (uint8_t) ~DTUNE0_PRE_PAC_SYM_BIT_MASK, config->rxPAC);

    dwt_write8bitoffsetreg(STS_CFG0_ID, 0, sts_len-1);    /*Starts from 0 that is why -1*/

    if (config->txPreambLength == DWT_PLEN_72)
    {
        dwt_setplenfine(8); //value 8 sets fine preamble length to 72 symbols - this is needed to set 72 length.
    }
    else
    {
        dwt_setplenfine(0); //clear the setting in the FINE_PLEN register.
    }

    if((config->stsMode & DWT_STS_MODE_ND) == DWT_STS_MODE_ND)
    {
        //configure lower preamble detection threshold for no data STS mode
        dwt_write32bitoffsetreg(DTUNE3_ID, 0, PD_THRESH_NO_DATA);
    }
    else
    {
        //configure default preamble detection threshold for other modes
        dwt_write32bitoffsetreg(DTUNE3_ID, 0, PD_THRESH_DEFAULT);
    }

    /////////////////////////////////////////////////////////////////////////
    //CHAN_CTRL
    temp = dwt_read32bitoffsetreg(CHAN_CTRL_ID, 0);
    temp &= (~(CHAN_CTRL_RX_PCODE_BIT_MASK | CHAN_CTRL_TX_PCODE_BIT_MASK | CHAN_CTRL_SFD_TYPE_BIT_MASK | CHAN_CTRL_RF_CHAN_BIT_MASK));

    if (chan == 9) temp |= CHAN_CTRL_RF_CHAN_BIT_MASK;

    temp |= (CHAN_CTRL_RX_PCODE_BIT_MASK & ((uint32_t)config->rxCode << CHAN_CTRL_RX_PCODE_BIT_OFFSET));
    temp |= (CHAN_CTRL_TX_PCODE_BIT_MASK & ((uint32_t)config->txCode << CHAN_CTRL_TX_PCODE_BIT_OFFSET));
    temp |= (CHAN_CTRL_SFD_TYPE_BIT_MASK & ((uint32_t)config->sfdType << CHAN_CTRL_SFD_TYPE_BIT_OFFSET));

    dwt_write32bitoffsetreg(CHAN_CTRL_ID, 0, temp);

    /////////////////////////////////////////////////////////////////////////
    //TX_FCTRL
    // Set up TX Preamble Size, PRF and Data Rate
    dwt_modify32bitoffsetreg(TX_FCTRL_ID, 0, ~(TX_FCTRL_TXBR_BIT_MASK | TX_FCTRL_TXPSR_BIT_MASK),
                                              ((uint32_t)config->dataRate << TX_FCTRL_TXBR_BIT_OFFSET)
                                              | ((uint32_t) config->txPreambLength) << TX_FCTRL_TXPSR_BIT_OFFSET);


    //DTUNE (SFD timeout)
    // Don't allow 0 - SFD timeout will always be enabled
    if (config->sfdTO == 0)
    {
        config->sfdTO = DWT_SFDTOC_DEF;
    }
    dwt_write16bitoffsetreg(DTUNE0_ID, 2, config->sfdTO);


    ///////////////////////
    // RF
    if (chan == 9)
    {
        // Setup TX analog for ch9
        dwt_write32bitoffsetreg(TX_CTRL_HI_ID, 0, RF_TXCTRL_CH9);
        dwt_write16bitoffsetreg(PLL_CFG_ID, 0, RF_PLL_CFG_CH9);
        // Setup RX analog for ch9
        dwt_write32bitoffsetreg(RX_CTRL_HI_ID, 0, RF_RXCTRL_CH9);
    }
    else
    {
        // Setup TX analog for ch5
        dwt_write32bitoffsetreg(TX_CTRL_HI_ID, 0, RF_TXCTRL_CH5);
        dwt_write16bitoffsetreg(PLL_CFG_ID, 0, RF_PLL_CFG_CH5);
    }

    dwt_write8bitoffsetreg(LDO_RLOAD_ID, 1, LDO_RLOAD_VAL_B1);
    dwt_write8bitoffsetreg(TX_CTRL_LO_ID, 2, RF_TXCTRL_LO_B2);
    dwt_write8bitoffsetreg(PLL_CAL_ID, 0, RF_PLL_CFG_LD);        // Extend the lock delay

    //Verify PLL lock bit is cleared
    dwt_write8bitoffsetreg(SYS_STATUS_ID, 0, SYS_STATUS_CP_LOCK_BIT_MASK);

    ///////////////////////
    // auto cal the PLL and change to IDLE_PLL state
    dwt_setdwstate(DWT_DW_IDLE);

    for (flag=1, cnt=0; cnt < MAX_RETRIES_FOR_PLL; cnt++)
    {
        deca_usleep(DELAY_20uUSec);
        if ((dwt_read8bitoffsetreg(SYS_STATUS_ID, 0) & SYS_STATUS_CP_LOCK_BIT_MASK))
        {
            /* PLL is locked */
            flag = 0;
            break;
        }
    }
    if (flag)
    {
        return  DWT_ERROR;
    }

    if ((config->rxCode >= 9) && (config->rxCode <= 24)) //only enable DGC for PRF 64
    {
        //load RX LUTs
        /* If the OTP has DGC info programmed into it, do a manual kick from OTP. */
        if (pdw3000local->dgc_otp_set == DWT_DGC_LOAD_FROM_OTP)
        {
            _dwt_kick_dgc_on_wakeup(chan);
        }
        /* Else we manually program hard-coded values into the DGC registers. */
        else
        {
            dwt_configmrxlut(chan);
        }
        dwt_modify16bitoffsetreg(DGC_CFG_ID, 0x0, (uint16_t)~DGC_CFG_THR_64_BIT_MASK, DWT_DGC_CFG << DGC_CFG_THR_64_BIT_OFFSET);
    }
    else
    {
        dwt_and8bitoffsetreg(DGC_CFG_ID, 0x0, (uint8_t)~DGC_CFG_RX_TUNE_EN_BIT_MASK);
    }

    ///////////////////////
    // PGF
    error = dwt_pgf_cal(1);  //if the RX calibration routine fails the device receiver performance will be severely affected, the application should reset and try again


    return error;
} // end dwt_configure()

/*! ------------------------------------------------------------------------------------------------------------------
 *
 * @brief This function runs the PGF calibration. This is needed prior to reception.
 * Note: If the RX calibration routine fails the device receiver performance will be severely affected, the application should reset and try again
 *
 * input parameters
 * @param ldoen    -   if set to 1 the function will enable LDOs prior to calibration and disable afterwards.
 *
 * return result of PGF calibration (DWT_ERROR/-1 = error)
 *
 */
int dwt_pgf_cal(int ldoen)
{
    int temp;
    uint16_t val;

    //PGF needs LDOs turned on - ensure PGF LDOs are enabled
    if (ldoen == 1)
    {
        val = dwt_read16bitoffsetreg(LDO_CTRL_ID, 0);

        dwt_or16bitoffsetreg(LDO_CTRL_ID, 0, (
            LDO_CTRL_LDO_VDDIF2_EN_BIT_MASK |
            LDO_CTRL_LDO_VDDMS3_EN_BIT_MASK |
            LDO_CTRL_LDO_VDDMS1_EN_BIT_MASK));
    }

    //Run PGF Cal
    temp = dwt_run_pgfcal();

    //Turn off RX LDOs if previously off
    if (ldoen == 1)
    {
        dwt_and16bitoffsetreg(LDO_CTRL_ID, 0, val); // restore LDO values
    }
    return temp;
}

/*! ------------------------------------------------------------------------------------------------------------------
 *
 * @brief This function runs the PGF calibration. This is needed prior to reception.
 *
 * input parameters
 *
 * return result of PGF calibration (DWT_ERROR/-1 = error)
 *
 */
int dwt_run_pgfcal(void)
{
    int result = DWT_SUCCESS;
    uint32_t    data;
    uint32_t    val = 0;
    uint8_t     cnt,flag;

    //put into cal mode
    //Turn on delay mode
    data = (((uint32_t)0x02) << RX_CAL_CFG_COMP_DLY_BIT_OFFSET) | (RX_CAL_CFG_CAL_MODE_BIT_MASK & 0x1);
    dwt_write32bitoffsetreg(RX_CAL_CFG_ID, 0x0, data);
    // Trigger PGF Cal
    dwt_or8bitoffsetreg(RX_CAL_CFG_ID, 0x0, RX_CAL_CFG_CAL_EN_BIT_MASK);

    for (flag=1,cnt=0;cnt<MAX_RETRIES_FOR_PGF;cnt++)
    {
        deca_usleep(DELAY_20uUSec);
        if(dwt_read8bitoffsetreg(RX_CAL_STS_ID, 0x0) == 1)
        {//PGF cal is complete
            flag=0;
            break;
        }
    }
    if (flag)
    {
        result = DWT_ERROR;
    }

    // Put into normal mode
    dwt_write8bitoffsetreg(RX_CAL_CFG_ID, 0x0, 0);
    dwt_write8bitoffsetreg(RX_CAL_STS_ID, 0x0, 1); //clear the status
    dwt_or8bitoffsetreg(RX_CAL_CFG_ID, 0x2, 0x1); //enable reading
    val = dwt_read32bitoffsetreg(RX_CAL_RESI_ID, 0x0);
    if (val == ERR_RX_CAL_FAIL)
    {
        //PGF I Cal Fail
        result = DWT_ERROR;
    }
    val = dwt_read32bitoffsetreg(RX_CAL_RESQ_ID, 0x0);
    if (val == ERR_RX_CAL_FAIL)
    {
        //PGF Q Cal Fail
        result = DWT_ERROR;
    }

    return result;
}

/*! ------------------------------------------------------------------------------------------------------------------
 * @brief This API function writes the antenna delay (in time units) to RX registers
 *
 * input parameters:
 * @param rxDelay - this is the total (RX) antenna delay value, which
 *                          will be programmed into the RX register
 *
 * output parameters
 *
 * no return value
 */
void dwt_setrxantennadelay(uint16_t rxDelay)
{
    // Set the RX antenna delay for auto TX timestamp adjustment
    dwt_write16bitoffsetreg(CIA_CONF_ID, 0, rxDelay);
}

/*! ------------------------------------------------------------------------------------------------------------------
 * @brief This API function writes the antenna delay (in time units) to TX registers
 *
 * input parameters:
 * @param txDelay - this is the total (TX) antenna delay value, which
 *                          will be programmed into the TX delay register
 *
 * output parameters
 *
 * no return value
 */
void dwt_settxantennadelay(uint16_t txDelay)
{
    // Set the TX antenna delay for auto TX timestamp adjustment
    dwt_write16bitoffsetreg(TX_ANTD_ID, 0, txDelay);
}

/*! ------------------------------------------------------------------------------------------------------------------
 * @brief This API function writes the supplied TX data into the DW3000's
 * TX buffer.  The input parameters are the data length in bytes and a pointer
 * to those data bytes.
 *
 * input parameters
 * @param txDataLength   - This is the total length of data (in bytes) to write to the tx buffer.
 *                         Note: the size of tx buffer is 1024 bytes.
 *                         The standard PHR mode allows to transmit frames of up to 127 bytes (including 2 byte CRC)
 *                         The extended PHR mode allows to transmit frames of up to 1023 bytes (including 2 byte CRC)
 *                         if > 127 is programmed, DWT_PHRMODE_EXT needs to be set in the phrMode configuration
 *                         see dwt_configure function
 * @param txDataBytes    - Pointer to the user's buffer containing the data to send.
 * @param txBufferOffset - This specifies an offset in the DW IC's TX Buffer at which to start writing data.
 *
 * output parameters
 *
 * returns DWT_SUCCESS for success, or DWT_ERROR for error
 */
int dwt_writetxdata(uint16_t txDataLength, uint8_t *txDataBytes, uint16_t txBufferOffset)
{
#ifdef DWT_API_ERROR_CHECK
    assert((pdw3000local->longFrames && (txDataLength <= EXT_FRAME_LEN)) ||\
           (txDataLength <= STD_FRAME_LEN));
    assert((txBufferOffset + txDataLength) < TX_BUFFER_MAX_LEN);
#endif

    if ((txBufferOffset + txDataLength) < TX_BUFFER_MAX_LEN)
    {
        if(txBufferOffset <= REG_DIRECT_OFFSET_MAX_LEN)
        {
            /* Directly write the data to the IC TX buffer */
            dwt_writetodevice(TX_BUFFER_ID, txBufferOffset, txDataLength, txDataBytes);
        }
        else
        {
            /* Program the indirect offset register A for specified offset to TX buffer */
            dwt_write32bitreg(INDIRECT_ADDR_A_ID, (TX_BUFFER_ID >> 16) );
            dwt_write32bitreg(ADDR_OFFSET_A_ID,   txBufferOffset);

            /* Indirectly write the data to the IC TX buffer */
            dwt_writetodevice(INDIRECT_POINTER_A_ID, 0, txDataLength, txDataBytes);
        }
        return DWT_SUCCESS;
    }
    else
        return DWT_ERROR;
} // end dwt_writetxdata()

/*! ------------------------------------------------------------------------------------------------------------------
 * @brief This API function configures the TX frame control register before the transmission of a frame
 *
 * input parameters:
 * @param txFrameLength - this is the length of TX message (including the 2 byte CRC) - max is 1023
 *                              NOTE: standard PHR mode allows up to 127 bytes
 *                              if > 127 is programmed, DWT_PHRMODE_EXT needs to be set in the phrMode configuration
 *                              see dwt_configure function
 * @param txBufferOffset - the offset in the tx buffer to start writing the data
 * @param ranging - 1 if this is a ranging frame, else 0
 *
 * output parameters
 *
 * no return value
 */
void dwt_writetxfctrl(uint16_t txFrameLength, uint16_t txBufferOffset, uint8_t ranging)
{
    uint32_t reg32;
#ifdef DWT_API_ERROR_CHECK
    assert((pdw3000local->longFrames && (txFrameLength <= EXT_FRAME_LEN)) ||\
           (txFrameLength <= STD_FRAME_LEN));
#endif

    //DW3000/3700 - if offset is > 127, 128 needs to be added before data is written, this will be subtracted internally
    //prior to writing the data
    if(txBufferOffset <= 127)
    {
        // Write the frame length to the TX frame control register
        reg32 = txFrameLength | ((uint32_t)(txBufferOffset) << TX_FCTRL_TXB_OFFSET_BIT_OFFSET) | ((uint32_t)ranging << TX_FCTRL_TR_BIT_OFFSET);
        dwt_modify32bitoffsetreg(TX_FCTRL_ID, 0, ~(TX_FCTRL_TXB_OFFSET_BIT_MASK | TX_FCTRL_TR_BIT_MASK | TX_FCTRL_TXFLEN_BIT_MASK), reg32);
    }
    else
    {
        // Write the frame length to the TX frame control register
        reg32 = txFrameLength | ((uint32_t)(txBufferOffset + DWT_TX_BUFF_OFFSET_ADJUST) << TX_FCTRL_TXB_OFFSET_BIT_OFFSET) | ((uint32_t)ranging << TX_FCTRL_TR_BIT_OFFSET);
        dwt_modify32bitoffsetreg(TX_FCTRL_ID, 0, ~(TX_FCTRL_TXB_OFFSET_BIT_MASK | TX_FCTRL_TR_BIT_MASK | TX_FCTRL_TXFLEN_BIT_MASK), reg32);
        reg32 = dwt_read8bitoffsetreg(SAR_CTRL_ID, 0); //DW3000/3700 - need to read this to load the correct TX buffer offset value
    }

} // end dwt_writetxfctrl()

/*! ------------------------------------------------------------------------------------------------------------------
* @brief This API function is used to configure frame preamble length, the frame premable length can be
* configured in steps of 8, from 16 to 2048 symbols. If a non-zero value is configured, then the TXPSR_PE setting is ignored.
*
* input parameters:
* @param preambleLength - sets the length of the preamble, value of 0 disables this setting and the length of the
*                         frame will be dependent on the TXPSR_PE setting as configured by dwt_configure function
*
* output parameters
*
* no return value
*/
void dwt_setplenfine(uint8_t preambleLength)
{
    dwt_write8bitoffsetreg(TX_FCTRL_HI_ID, 1, preambleLength);
}

/*! ------------------------------------------------------------------------------------------------------------------
 * @brief This is used to read the data from the RX scratch buffer, from an offset location given by offset parameter.
 *
 * input parameters
 * @param buffer - the buffer into which the data will be read
 * @param length - the length of data to read (in bytes)
 * @param rxBufferOffset - the offset in the rx buffer from which to read the data
 *
 * output parameters
 *
 * no return value
 */
void dwt_read_rx_scratch_data(uint8_t *buffer, uint16_t length, uint16_t rxBufferOffset)
{
    //!!Check later if needs range protection.

    /* Directly read data from the IC to the buffer */
    dwt_readfromdevice(SCRATCH_RAM_ID,rxBufferOffset,length,buffer);
}

/*! ------------------------------------------------------------------------------------------------------------------
 * @brief This is used to read the data from the RX buffer, from an offset location give by offset parameter
 *
 * input parameters
 * @param buffer - the buffer into which the data will be read
 * @param length - the length of data to read (in bytes)
 * @param rxBufferOffset - the offset in the rx buffer from which to read the data
 *
 * output parameters
 *
 * no return value
 */
void dwt_readrxdata(uint8_t *buffer, uint16_t length, uint16_t rxBufferOffset)
{
    uint32_t  rx_buff_addr;

    if (pdw3000local->dblbuffon == DBL_BUFF_ACCESS_BUFFER_1)  //if the flag is 0x3 we are reading from RX_BUFFER_1
    {
        rx_buff_addr=RX_BUFFER_1_ID;
    }
    else //reading from RX_BUFFER_0 - also when non-double buffer mode
    {
        rx_buff_addr=RX_BUFFER_0_ID;
    }

    if ((rxBufferOffset + length) <= RX_BUFFER_MAX_LEN)
    {
        if(rxBufferOffset <= REG_DIRECT_OFFSET_MAX_LEN)
        {
            /* Directly read data from the IC to the buffer */
            dwt_readfromdevice(rx_buff_addr,rxBufferOffset,length,buffer);
        }
        else
        {
            /* Program the indirect offset registers B for specified offset to RX buffer */
            dwt_write32bitreg(INDIRECT_ADDR_A_ID, (rx_buff_addr >> 16) );
            dwt_write32bitreg(ADDR_OFFSET_A_ID,   rxBufferOffset);

            /* Indirectly read data from the IC to the buffer */
            dwt_readfromdevice(INDIRECT_POINTER_A_ID, 0, length, buffer);
        }
    }
}

/*! ------------------------------------------------------------------------------------------------------------------
 * @brief This is used to read the 18 bit data from the Accumulator buffer, from an offset location give by offset parameter
 *        for 18 bit complex samples, each sample is 6 bytes (3 real and 3 imaginary)
 *
 *
 * NOTE: Because of an internal memory access delay when reading the accumulator the first octet output is a dummy octet
 *       that should be discarded. This is true no matter what sub-index the read begins at.
 *
 * input parameters
 * @param buffer - the buffer into which the data will be read
 * @param length - the length of data to read (in bytes)
 * @param accOffset - the offset in the acc buffer from which to read the data, this is a complex sample index
 *                    e.g. to read 10 samples starting at sample 100
 *                    buffer would need to be >= 10*6 + 1, length is 61 (1 is for dummy), accOffset is 100
 *
 * output parameters
 *
 * no return value
 */
void dwt_readaccdata(uint8_t *buffer, uint16_t length, uint16_t accOffset)
{
    // Force on the ACC clocks if we are sequenced
    dwt_or16bitoffsetreg(CLK_CTRL_ID, 0x0, CLK_CTRL_ACC_MCLK_EN_BIT_MASK | CLK_CTRL_ACC_CLK_EN_BIT_MASK);

    if ((accOffset + length) <= ACC_BUFFER_MAX_LEN)
    {
        if(accOffset <= REG_DIRECT_OFFSET_MAX_LEN)
        {
            /* Directly read data from the IC to the buffer */
            dwt_readfromdevice(ACC_MEM_ID, accOffset, length, buffer);
        }
        else
        {
            /* Program the indirect offset registers B for specified offset to ACC */
            dwt_write32bitreg(INDIRECT_ADDR_A_ID, (ACC_MEM_ID >> 16) );
            dwt_write32bitreg(ADDR_OFFSET_A_ID,   accOffset);

            /* Indirectly read data from the IC to the buffer */
            dwt_readfromdevice(INDIRECT_POINTER_A_ID, 0, length, buffer);
        }
    }
    else
    {
        assert(0);
    }

    // Revert clocks back
    dwt_and16bitoffsetreg(CLK_CTRL_ID, 0x0, (uint16_t)~(CLK_CTRL_ACC_MCLK_EN_BIT_MASK | CLK_CTRL_ACC_CLK_EN_BIT_MASK));
}

/*! ------------------------------------------------------------------------------------------------------------------
 * @brief This is used to read the crystal offset (relating to the frequency offset of the far DW3000 device compared to this one)
 *        Note: the returned signed 16-bit number should be divided by by 2^26 to get ppm offset.
 *
 * input parameters - NONE
 *
 * return value - the (int12) signed offset value. (s[-15:-26])
 *                A positive value means the local RX clock is running faster than the remote TX device.
 */
int16_t dwt_readclockoffset(void)
{
    uint16_t  regval = 0 ;

    switch (pdw3000local->dblbuffon)  //if the flag is non zero - we are either accessing RX_BUFFER_0 or RX_BUFFER_1
    {
    case DBL_BUFF_ACCESS_BUFFER_1:
        //!!! Assumes that Indirect pointer register B was already set. This is done in the dwt_setdblrxbuffmode when mode is enabled.
        regval = dwt_read16bitoffsetreg(INDIRECT_POINTER_B_ID, (BUF1_CIA_DIAG_0-BUF1_RX_FINFO)) & CIA_DIAG_0_COE_PPM_BIT_MASK;
        break;
    case DBL_BUFF_ACCESS_BUFFER_0:
        regval = dwt_read16bitoffsetreg(BUF0_CIA_DIAG_0, 0) & CIA_DIAG_0_COE_PPM_BIT_MASK;
        break;
    default:
        regval = dwt_read16bitoffsetreg(CIA_DIAG_0_ID, 0) & CIA_DIAG_0_COE_PPM_BIT_MASK;
        break;
    }

    if (regval & B11_SIGN_EXTEND_TEST)
    {
        regval |= B11_SIGN_EXTEND_MASK;             // sign extend bit #12 to the whole short
    }

    return (int16_t) regval ;
}

/*! ------------------------------------------------------------------------------------------------------------------
 * @brief This is used to read the RX carrier integrator value (relating to the frequency offset of the TX node)
 *
 * NOTE: This is a 21-bit signed quantity, the function sign extends the most significant bit, which is bit #20
 *       (numbering from bit zero) to return a 32-bit signed integer value.
 *
 * input parameters - NONE
 *
 * return value - the (int32_t) signed carrier integrator value.
 *                A positive value means the local RX clock is running slower than the remote TX device.
 */
int32_t dwt_readcarrierintegrator(void)
{
    uint32_t  regval = 0 ;

    int     j ;
    uint8_t   buffer[DRX_CARRIER_INT_LEN] ;

    /* Read 3 bytes into buffer (21-bit quantity) */
    dwt_readfromdevice(DRX_DIAG3_ID, 0, DRX_CARRIER_INT_LEN, buffer);//

    for (j = 2 ; j >= 0 ; j --)  // arrange the three bytes into an unsigned integer value
    {
        regval = (regval << 8) + buffer[j] ;
    }

    if (regval & B20_SIGN_EXTEND_TEST)
    {
        regval |= B20_SIGN_EXTEND_MASK; // sign extend bit #20 to whole word
    }

    return (int32_t) regval ; // cast unsigned value to signed quantity.
}

/*! ------------------------------------------------------------------------------------------------------------------
 * @brief this function reads the STS signal quality index
 *
 * input parameters
 * @param rxStsQualityIndex - the (int16_t) signed STS quality index value.
 *
 * output parameters
 * return value - >=0 for good and < 0 if bad STS quality.
 *
 * Note: For the 64 MHz PRF if value is >= 90% of the STS length then we can assume good STS reception.
 *       Otherwise the STS timestamp may not be accurate.
 */
int dwt_readstsquality(int16_t* rxStsQualityIndex)
{
    uint16_t preambleCount;

    //read STS preamble count value
    preambleCount = dwt_read16bitoffsetreg(STS_STS_ID, 0) & STS_STS_ACC_QUAL_BIT_MASK; //  dwt_read16bitoffsetreg(CP_PRNG_ID, CP_STS_OFFSET) & CP_ACC_CP_QUAL_MASK;

    if(preambleCount & STS_ACC_CP_QUAL_SIGNTST)
        preambleCount |= STS_ACC_CP_QUAL_SIGNEXT;

    *rxStsQualityIndex = (int16_t)preambleCount;

    //determine if the STS Rx quality is good or bad (return >=0 for good and < 0 if bad)
    return (int)((int16_t)preambleCount - pdw3000local->ststhreshold);
}

/*! ------------------------------------------------------------------------------------------------------------------
 * @brief this function reads the STS status
 *
 * input parameters
 * @param stsStatus - the (uint16_t) STS status value. 9 bits of this buffer are populated with various STS statuses. The
 *                    remaining 7 bits are ignored.
 * @param sts_num   - 0 for 1st STS, 1 for 2nd STS (2nd only valid when PDOA Mode 3 is used)
 *
 * output parameters
 * return value DWT_SUCCESS for good/valid STS status, DWT_ERROR if bad STS status.
 */
int dwt_readstsstatus(uint16_t* stsStatus, int sts_num)
{
    int ret = DWT_SUCCESS;
    uint32_t stsStatusRegAdd = (sts_num == 1) ? BUF0_STS1_STAT : BUF0_STS_STAT;
    uint32_t stsStatusRegAddN = (sts_num == 1) ? STS1_TOA_HI_ID : STS_TOA_HI_ID;

    switch (pdw3000local->dblbuffon) //check if in double buffer mode and if so which buffer host is currently accessing
    {
    case DBL_BUFF_ACCESS_BUFFER_1:
        //!!! Assumes that Indirect pointer register B was already set. This is done in the dwt_setdblrxbuffmode when mode is enabled.
        *stsStatus = dwt_read16bitoffsetreg(INDIRECT_POINTER_B_ID, (stsStatusRegAdd-BUF0_RX_FINFO+2)) >> 7;
        break;
    case DBL_BUFF_ACCESS_BUFFER_0:
        *stsStatus = (dwt_read16bitoffsetreg(stsStatusRegAdd, 2) >> 7);
        break;
    default:
        *stsStatus = (dwt_read16bitoffsetreg(stsStatusRegAddN, 2) >> 7);
        break;
    }

    //determine if the STS is ok
    if (*stsStatus != 0 /*& DWT_SFD_COUNT_WARN*/)
        ret = DWT_ERROR;

    return ret;
}

/*! ------------------------------------------------------------------------------------------------------------------
 * @brief this function reads the RX signal quality diagnostic data
 *
 * input parameters
 * @param diagnostics - diagnostic structure pointer, this will contain the diagnostic data read from the DW3000
 *
 * output parameters
 *
 * no return value
 */
void dwt_readdiagnostics(dwt_rxdiag_t *diagnostics)
{
    int i;
    int offset_0xd;
    int offset_buff = BUF0_RX_FINFO;
    uint8_t temp[DB_MAX_DIAG_SIZE];  //address from 0xC0000 to 0xD0068 (108*2 bytes) - when using normal mode, or 232 length for max logging when in Double Buffer mode

    //minimal diagnostics - 40 bytes

    switch (pdw3000local->dblbuffon) //check if in double buffer mode and if so which buffer host is currently accessing
    {
    case DBL_BUFF_ACCESS_BUFFER_1:
        offset_buff = BUF1_RX_FINFO;
        __attribute__ ((fallthrough));
        //no break
    case DBL_BUFF_ACCESS_BUFFER_0:

        if (pdw3000local->dblbuffon == DBL_BUFF_ACCESS_BUFFER_1)
        {
            /* Program the indirect offset registers B for specified offset to swinging set buffer B */
            //!!! Assumes that Indirect pointer register B was already set. This is done in the dwt_setdblrxbuffmode when mode is enabled.
            /* Indirectly read data from the IC to the buffer */
            if (pdw3000local->cia_diagnostic & DW_CIA_DIAG_LOG_MAX)
            {
                dwt_readfromdevice(INDIRECT_POINTER_B_ID, 0, DB_MAX_DIAG_SIZE, temp);
            }
            else if (pdw3000local->cia_diagnostic & DW_CIA_DIAG_LOG_MID)
            {
                dwt_readfromdevice(INDIRECT_POINTER_B_ID, 0, DB_MID_DIAG_SIZE, temp);
            }
            else
            {
                dwt_readfromdevice(INDIRECT_POINTER_B_ID, 0, DB_MIN_DIAG_SIZE, temp);
            }
        }
        else
        {
            if (pdw3000local->cia_diagnostic & DW_CIA_DIAG_LOG_MAX)
            {
                dwt_readfromdevice(offset_buff, 0, DB_MAX_DIAG_SIZE, temp);
            }
            else if (pdw3000local->cia_diagnostic & DW_CIA_DIAG_LOG_MID)
            {
                dwt_readfromdevice(offset_buff, 0, DB_MID_DIAG_SIZE, temp);
            }
            else
            {
                dwt_readfromdevice(offset_buff, 0, DB_MIN_DIAG_SIZE, temp);
            }
        }

        for (i = 0; i < (CIA_I_RX_TIME_LEN+1); i++)
        {
            diagnostics->tdoa[i] = temp[i + BUF0_TDOA - BUF0_RX_FINFO]; // timestamp difference of the 2 STS RX timestamps
        }

        diagnostics->xtalOffset = ((int16_t)temp[BUF0_CIA_DIAG_0 - BUF0_RX_FINFO + 1] << 8 | temp[BUF0_CIA_DIAG_0 - BUF0_RX_FINFO]) & 0x1FFF;                   // Estimated xtal offset of remote device

        diagnostics->pdoa = ((int16_t)temp[BUF0_PDOA - BUF0_RX_FINFO + 3] << 8 | temp[BUF0_PDOA - BUF0_RX_FINFO + 2]) & 0x3FFF;           // phase difference of the 2 STS POAs (signed in [1:-11])
        if (diagnostics->pdoa & 0x2000) diagnostics->pdoa |= 0xC000; //sign extend

        diagnostics->ipatovAccumCount = ((uint16_t)temp[BUF0_IP_DIAG_12 - BUF0_RX_FINFO + 1] << 8 | temp[BUF0_IP_DIAG_12 - BUF0_RX_FINFO]) & 0xFFF;       // Number accumulated symbols [11:0] for Ipatov sequence

        if (pdw3000local->cia_diagnostic & DW_CIA_DIAG_LOG_MIN)
            break;

        for (i = 0; i < CIA_I_RX_TIME_LEN; i++)
        {
            diagnostics->ipatovRxTime[i] = temp[i + BUF0_IP_TS - BUF0_RX_FINFO];  // RX timestamp from Ipatov sequence
            diagnostics->stsRxTime[i] = temp[i + BUF0_STS_TS - BUF0_RX_FINFO];    // RX timestamp from STS
            diagnostics->sts2RxTime[i] = temp[i + BUF0_STS1_TS - BUF0_RX_FINFO];  // RX timestamp from STS1
        }
        diagnostics->ipatovRxStatus = temp[BUF0_IP_TS - BUF0_RX_FINFO + CIA_C_STAT_OFFSET];        // RX status info for Ipatov sequence
        diagnostics->ipatovPOA = (uint16_t)temp[BUF0_IP_TS - BUF0_RX_FINFO + 2] << 8 | temp[BUF0_IP_TS - BUF0_RX_FINFO + 1]; // Phase of arrival as computed from the Ipatov CIR (signed rad*2-12)

        diagnostics->stsRxStatus = temp[BUF0_STS_TS - BUF0_RX_FINFO + CIA_C_STAT_OFFSET];       // RX status info for STS
        diagnostics->stsPOA = (uint16_t)temp[BUF0_STS_TS - BUF0_RX_FINFO + 2] << 8 | temp[BUF0_STS_TS - BUF0_RX_FINFO + 1]; // Phase of arrival as computed from the STS 1 CIR (signed rad*2-12)

        diagnostics->sts2RxStatus = temp[BUF0_STS1_TS - BUF0_RX_FINFO + CIA_C_STAT_OFFSET];       // RX status info for STS1
        diagnostics->sts2POA = (uint16_t)temp[BUF0_STS1_TS - BUF0_RX_FINFO + 2] << 8 | temp[BUF0_STS1_TS - BUF0_RX_FINFO + 1]; // Phase of arrival as computed from the STS 1 CIR (signed rad*2-12)

        if (pdw3000local->cia_diagnostic & DW_CIA_DIAG_LOG_MID)
            break;

        diagnostics->ciaDiag1 = ((uint32_t)temp[BUF0_CIA_DIAG_1 - BUF0_RX_FINFO + 3] << 24 | (uint32_t)temp[BUF0_CIA_DIAG_1 - BUF0_RX_FINFO + 2] << 16
            | (uint32_t)temp[BUF0_CIA_DIAG_1 - BUF0_RX_FINFO + 1] << 8 | (uint32_t)temp[BUF0_CIA_DIAG_1 - BUF0_RX_FINFO]) & 0x1FFFFFFF; // Diagnostics common to both sequences (carrier integrator [28:8] and resampler delay [7:0])

                                                                                                                          //IP
        diagnostics->ipatovPeak = ((uint32_t)temp[BUF0_IP_DIAG_0 - BUF0_RX_FINFO + 3] << 24 | (uint32_t)temp[BUF0_IP_DIAG_0 - BUF0_RX_FINFO + 2] << 16
            | (uint32_t)temp[BUF0_IP_DIAG_0 - BUF0_RX_FINFO + 1] << 8 | (uint32_t)temp[BUF0_IP_DIAG_0 - BUF0_RX_FINFO]) & 0x7FFFFFFF;  // index [30:21] and amplitude [20:0] of peak sample in Ipatov sequence CIR
        diagnostics->ipatovPower = ((uint32_t)temp[BUF0_IP_DIAG_1 - BUF0_RX_FINFO + 3] << 24 | (uint32_t)temp[BUF0_IP_DIAG_1 - BUF0_RX_FINFO + 2] << 16
            | (uint32_t)temp[BUF0_IP_DIAG_1 - BUF0_RX_FINFO + 1] << 8 | (uint32_t)temp[BUF0_IP_DIAG_1 - BUF0_RX_FINFO]) & 0x1FFFF;     // channel area allows estimation [16:0] of channel power for the Ipatov sequence
        diagnostics->ipatovF1 = ((uint32_t)temp[BUF0_IP_DIAG_2 - BUF0_RX_FINFO + 3] << 24 | (uint32_t)temp[BUF0_IP_DIAG_2 - BUF0_RX_FINFO + 2] << 16
            | (uint32_t)temp[BUF0_IP_DIAG_2 - BUF0_RX_FINFO + 1] << 8 | (uint32_t)temp[BUF0_IP_DIAG_2 - BUF0_RX_FINFO]) & 0x3FFFFF;    // F1 for Ipatov sequence [21:0]
        diagnostics->ipatovF2 = ((uint32_t)temp[BUF0_IP_DIAG_3 - BUF0_RX_FINFO + 3] << 24 | (uint32_t)temp[BUF0_IP_DIAG_3 - BUF0_RX_FINFO + 2] << 16
            | (uint32_t)temp[BUF0_IP_DIAG_3 - BUF0_RX_FINFO + 1] << 8 | (uint32_t)temp[BUF0_IP_DIAG_3 - BUF0_RX_FINFO]) & 0x3FFFFF;    // F2 for Ipatov sequence [21:0]
        diagnostics->ipatovF3 = ((uint32_t)temp[BUF0_IP_DIAG_4 - BUF0_RX_FINFO + 3] << 24 | (uint32_t)temp[BUF0_IP_DIAG_4 - BUF0_RX_FINFO + 2] << 16
            | (uint32_t)temp[BUF0_IP_DIAG_4 - BUF0_RX_FINFO + 1] << 8 | (uint32_t)temp[BUF0_IP_DIAG_4 - BUF0_RX_FINFO]) & 0x3FFFFF;    // F3 for Ipatov sequence [21:0]
        diagnostics->ipatovFpIndex = (uint16_t)temp[BUF0_IP_DIAG_8 - BUF0_RX_FINFO + 1] << 8 | temp[BUF0_IP_DIAG_8 - BUF0_RX_FINFO];              // First path index [15:0] for Ipatov sequence

                                                                                                                                                  //CP 1
        diagnostics->stsPeak = ((uint32_t)temp[BUF0_STS_DIAG_0 - BUF0_RX_FINFO + 3] << 24 | (uint32_t)temp[BUF0_STS_DIAG_0 - BUF0_RX_FINFO + 2] << 16
            | (uint32_t)temp[BUF0_STS_DIAG_0 - BUF0_RX_FINFO + 1] << 8 | (uint32_t)temp[BUF0_STS_DIAG_0 - BUF0_RX_FINFO]) & 0x3FFFFFFF; // index [29:21] and amplitude [20:0] of peak sample in STS CIR
        diagnostics->stsPower = ((uint16_t)temp[BUF0_STS_DIAG_1 - BUF0_RX_FINFO + 1] << 8 | temp[BUF0_STS_DIAG_1 - BUF0_RX_FINFO]);           // channel area allows estimation of channel power for the STS
        diagnostics->stsF1 = ((uint32_t)temp[BUF0_STS_DIAG_2 - BUF0_RX_FINFO + 3] << 24 | (uint32_t)temp[BUF0_STS_DIAG_2 - BUF0_RX_FINFO + 2] << 16
            | (uint32_t)temp[BUF0_STS_DIAG_2 - BUF0_RX_FINFO + 1] << 8 | (uint32_t)temp[BUF0_STS_DIAG_2 - BUF0_RX_FINFO]) & 0x3FFFFF; // F1 for STS [21:0]
        diagnostics->stsF2 = ((uint32_t)temp[BUF0_STS_DIAG_3 - BUF0_RX_FINFO + 3] << 24 | (uint32_t)temp[BUF0_STS_DIAG_3 - BUF0_RX_FINFO + 2] << 16
            | (uint32_t)temp[BUF0_STS_DIAG_3 - BUF0_RX_FINFO + 1] << 8 | (uint32_t)temp[BUF0_STS_DIAG_3 - BUF0_RX_FINFO]) & 0x3FFFFF; // F2 for STS [21:0]
        diagnostics->stsF3 = ((uint32_t)temp[BUF0_STS_DIAG_4 - BUF0_RX_FINFO + 3] << 24 | (uint32_t)temp[BUF0_STS_DIAG_4 - BUF0_RX_FINFO + 2] << 16
            | (uint32_t)temp[BUF0_STS_DIAG_4 - BUF0_RX_FINFO + 1] << 8 | (uint32_t)temp[BUF0_STS_DIAG_4 - BUF0_RX_FINFO]) & 0x3FFFFF; // F3 for STS [21:0]
        diagnostics->stsFpIndex = ((uint16_t)temp[BUF0_STS_DIAG_8 - BUF0_RX_FINFO + 1] << 8 | temp[BUF0_STS_DIAG_8 - BUF0_RX_FINFO]) & 0x7FFF;   // First path index [14:0] for STS
        diagnostics->stsAccumCount = ((uint16_t)temp[BUF0_STS_DIAG_12 - BUF0_RX_FINFO + 1] << 8 | temp[BUF0_STS_DIAG_12 - BUF0_RX_FINFO]) & 0xFFF;   // Number accumulated symbols [11:0] for STS

                                                                                                                                                //CP 2
        diagnostics->sts2Peak = ((uint32_t)temp[BUF0_STS1_DIAG_0 - BUF0_RX_FINFO + 3] << 24 | (uint32_t)temp[BUF0_STS1_DIAG_0 - BUF0_RX_FINFO + 2] << 16
            | (uint32_t)temp[BUF0_STS1_DIAG_0 - BUF0_RX_FINFO + 1] << 8 | (uint32_t)temp[BUF0_STS1_DIAG_0 - BUF0_RX_FINFO]) & 0x3FFFFFFF; // index [29:21] and amplitude [20:0] of peak sample in STS CIR
        diagnostics->sts2Power = ((uint16_t)temp[BUF0_STS1_DIAG_1 - BUF0_RX_FINFO + 1] << 8 | temp[BUF0_STS1_DIAG_1 - BUF0_RX_FINFO]);           // channel area allows estimation of channel power for the STS
        diagnostics->sts2F1 = ((uint32_t)temp[BUF0_STS1_DIAG_2 - BUF0_RX_FINFO + 3] << 24 | (uint32_t)temp[BUF0_STS1_DIAG_2 - BUF0_RX_FINFO + 2] << 16
            | (uint32_t)temp[BUF0_STS1_DIAG_2 - BUF0_RX_FINFO + 1] << 8 | (uint32_t)temp[BUF0_STS1_DIAG_2 - BUF0_RX_FINFO]) & 0x3FFFFF; // F1 for STS [21:0]
        diagnostics->sts2F2 = ((uint32_t)temp[BUF0_STS1_DIAG_3 - BUF0_RX_FINFO + 3] << 24 | (uint32_t)temp[BUF0_STS1_DIAG_3 - BUF0_RX_FINFO + 2] << 16
            | (uint32_t)temp[BUF0_STS1_DIAG_3 - BUF0_RX_FINFO + 1] << 8 | (uint32_t)temp[BUF0_STS1_DIAG_3 - BUF0_RX_FINFO]) & 0x3FFFFF; // F2 for STS [21:0]
        diagnostics->sts2F3 = ((uint32_t)temp[BUF0_STS1_DIAG_4 - BUF0_RX_FINFO + 3] << 24 | (uint32_t)temp[BUF0_STS1_DIAG_4 - BUF0_RX_FINFO + 2] << 16
            | (uint32_t)temp[BUF0_STS1_DIAG_4 - BUF0_RX_FINFO + 1] << 8 | (uint32_t)temp[BUF0_STS1_DIAG_4 - BUF0_RX_FINFO]) & 0x3FFFFF; // F3 for STS [21:0]
        diagnostics->sts2FpIndex = ((uint16_t)temp[BUF0_STS1_DIAG_8 - BUF0_RX_FINFO + 1] << 8 | temp[BUF0_STS1_DIAG_8 - BUF0_RX_FINFO]) & 0x7FFF;   // First path index [14:0] for STS
        diagnostics->sts2AccumCount = ((uint16_t)temp[BUF0_STS1_DIAG_12 - BUF0_RX_FINFO + 1] << 8 | temp[BUF0_STS1_DIAG_12 - BUF0_RX_FINFO]) & 0xFFF;   // Number accumulated symbols [11:0] for STS



        break;

    default:  //double buffer is off

        if (pdw3000local->cia_diagnostic & DW_CIA_DIAG_LOG_ALL)
        {
            dwt_readfromdevice(IP_TOA_LO_ID, 0, 108, temp);   //read form 0xC0000 space  (108 bytes)
            dwt_readfromdevice(STS_DIAG_4_ID, 0, 108, &temp[108]);  //read from 0xD0000 space  (108 bytes)
        }
        else
        {
            dwt_readfromdevice(IP_TOA_LO_ID, 0, 40, temp);
        }

        for (i = 0; i < CIA_I_RX_TIME_LEN; i++)
        {
            diagnostics->ipatovRxTime[i] = temp[i];                                 // RX timestamp from Ipatov sequence
            diagnostics->stsRxTime[i] = temp[i + STS_TOA_LO_ID - IP_TOA_LO_ID];  // RX timestamp from STS
            diagnostics->sts2RxTime[i] = temp[i + STS1_TOA_LO_ID - IP_TOA_LO_ID]; // RX timestamp from STS1
            diagnostics->tdoa[i] = temp[i + CIA_TDOA_0_ID - IP_TOA_LO_ID]; // timestamp difference of the 2 STS RX timestamps
        }
        diagnostics->tdoa[5] = temp[5 + CIA_TDOA_0_ID - IP_TOA_LO_ID];

        diagnostics->ipatovRxStatus = temp[IP_TOA_HI_ID - IP_TOA_LO_ID + CIA_I_STAT_OFFSET];        // RX status info for Ipatov sequence
        diagnostics->ipatovPOA = (uint16_t)temp[IP_TOA_HI_ID - IP_TOA_LO_ID + 2] << 8 | temp[IP_TOA_HI_ID - IP_TOA_LO_ID + 1]; // Phase of arrival as computed from the Ipatov CIR (signed rad*2-12)

        diagnostics->stsRxStatus = ((uint16_t)temp[STS_TOA_HI_ID - IP_TOA_LO_ID + CIA_C_STAT_OFFSET + 1] | temp[STS_TOA_HI_ID - IP_TOA_LO_ID + CIA_C_STAT_OFFSET]) >> 7;       // RX status info for STS
        diagnostics->stsPOA = (uint16_t)temp[STS_TOA_HI_ID - IP_TOA_LO_ID + 2] << 8 | temp[STS_TOA_HI_ID - IP_TOA_LO_ID + 1]; // Phase of arrival as computed from the STS 1 CIR (signed rad*2-12)

        diagnostics->sts2RxStatus = ((uint16_t)temp[STS1_TOA_HI_ID - IP_TOA_LO_ID + CIA_C_STAT_OFFSET+ 1] | temp[STS_TOA_HI_ID - IP_TOA_LO_ID + CIA_C_STAT_OFFSET]) >> 7;       // RX status info for STS
        diagnostics->sts2POA = (uint16_t)temp[STS1_TOA_HI_ID - IP_TOA_LO_ID + 2] << 8 | temp[STS1_TOA_HI_ID - IP_TOA_LO_ID + 1]; // Phase of arrival as computed from the STS 1 CIR (signed rad*2-12)

        diagnostics->pdoa = ((int16_t)temp[CIA_TDOA_1_PDOA_ID - IP_TOA_LO_ID + 3] << 8 | temp[CIA_TDOA_1_PDOA_ID - IP_TOA_LO_ID + 2]) & 0x3FFF;           // phase difference of the 2 STS POAs (signed in [1:-11])
        if (diagnostics->pdoa & 0x2000) diagnostics->pdoa |= 0xC000; //sign extend

        diagnostics->xtalOffset = ((int16_t)temp[CIA_DIAG_0_ID - IP_TOA_LO_ID + 1] << 8 | temp[CIA_DIAG_0_ID - IP_TOA_LO_ID]) & 0x1FFF;                   // Estimated xtal offset of remote device

        diagnostics->ciaDiag1 = ((uint32_t) temp[CIA_DIAG_1_ID - IP_TOA_LO_ID + 3] << 24 | (uint32_t)temp[CIA_DIAG_1_ID - IP_TOA_LO_ID + 2] << 16
            | (uint32_t)temp[CIA_DIAG_1_ID - IP_TOA_LO_ID + 1] << 8 | (uint32_t)temp[CIA_DIAG_1_ID - IP_TOA_LO_ID]) & 0x1FFFFFFF; // Diagnostics common to both sequences

        if ((pdw3000local->cia_diagnostic & DW_CIA_DIAG_LOG_ALL) == 0)
            break; //break here is only logging minimal diagnositcs

        //IP
        diagnostics->ipatovPeak = ((uint32_t)temp[IP_DIAG_0_ID - IP_TOA_LO_ID + 3] << 24 | (uint32_t)temp[IP_DIAG_0_ID - IP_TOA_LO_ID + 2] << 16
            | (uint32_t)temp[IP_DIAG_0_ID - IP_TOA_LO_ID + 1] << 8 | (uint32_t)temp[IP_DIAG_0_ID - IP_TOA_LO_ID]) & 0x7FFFFFFF;  // index [30:21] and amplitude [20:0] of peak sample in Ipatov sequence CIR
        diagnostics->ipatovPower = ((uint32_t)temp[IP_DIAG_1_ID - IP_TOA_LO_ID + 3] << 24 | (uint32_t)temp[IP_DIAG_1_ID - IP_TOA_LO_ID + 2] << 16
            | (uint32_t)temp[IP_DIAG_1_ID - IP_TOA_LO_ID + 1] << 8 | (uint32_t)temp[IP_DIAG_1_ID - IP_TOA_LO_ID]) & 0x1FFFF;     // channel area allows estimation [16:0] of channel power for the Ipatov sequence
        diagnostics->ipatovF1 = ((uint32_t)temp[IP_DIAG_2_ID - IP_TOA_LO_ID + 3] << 24 | (uint32_t)temp[IP_DIAG_2_ID - IP_TOA_LO_ID + 2] << 16
            | (uint32_t)temp[IP_DIAG_2_ID - IP_TOA_LO_ID + 1] << 8 | (uint32_t)temp[IP_DIAG_2_ID - IP_TOA_LO_ID]) & 0x3FFFFF;    // F1 for Ipatov sequence [21:0]
        diagnostics->ipatovF2 = ((uint32_t)temp[IP_DIAG_3_ID - IP_TOA_LO_ID + 3] << 24 | (uint32_t)temp[IP_DIAG_3_ID - IP_TOA_LO_ID + 2] << 16
            | (uint32_t)temp[IP_DIAG_3_ID - IP_TOA_LO_ID + 1] << 8 | (uint32_t)temp[IP_DIAG_3_ID - IP_TOA_LO_ID]) & 0x3FFFFF;    // F2 for Ipatov sequence [21:0]
        diagnostics->ipatovF3 = ((uint32_t)temp[IP_DIAG_4_ID - IP_TOA_LO_ID + 3] << 24 | (uint32_t)temp[IP_DIAG_4_ID - IP_TOA_LO_ID + 2] << 16
            | (uint32_t)temp[IP_DIAG_4_ID - IP_TOA_LO_ID + 1] << 8 | (uint32_t)temp[IP_DIAG_4_ID - IP_TOA_LO_ID]) & 0x3FFFFF;    // F3 for Ipatov sequence [21:0]
        diagnostics->ipatovFpIndex = (uint16_t)temp[IP_DIAG_8_ID - IP_TOA_LO_ID + 1] << 8 | temp[IP_DIAG_8_ID - IP_TOA_LO_ID];              // First path index [15:0] for Ipatov sequence
        diagnostics->ipatovAccumCount = ((uint16_t)temp[IP_DIAG_12_ID - IP_TOA_LO_ID + 1] << 8 | temp[IP_DIAG_12_ID - IP_TOA_LO_ID]) & 0xFFF;       // Number accumulated symbols [11:0] for Ipatov sequence

        //STS 1
        diagnostics->stsPeak = ((uint32_t)temp[STS_DIAG_0_ID - IP_TOA_LO_ID + 3] << 24 | (uint32_t)temp[STS_DIAG_0_ID - IP_TOA_LO_ID + 2] << 16
            | (uint32_t)temp[STS_DIAG_0_ID - IP_TOA_LO_ID + 1] << 8 | (uint32_t)temp[STS_DIAG_0_ID - IP_TOA_LO_ID]) & 0x3FFFFFFF; // index [29:21] and amplitude [20:0] of peak sample in STS CIR
        diagnostics->stsPower = ((uint16_t)temp[STS_DIAG_1_ID - IP_TOA_LO_ID + 1] << 8 | temp[STS_DIAG_1_ID - IP_TOA_LO_ID]);           // channel area allows estimation of channel power for the STS
        diagnostics->stsF1 = ((uint32_t)temp[STS_DIAG_2_ID - IP_TOA_LO_ID + 3] << 24 | (uint32_t)temp[STS_DIAG_2_ID - IP_TOA_LO_ID + 2] << 16
            | (uint32_t)temp[STS_DIAG_2_ID - IP_TOA_LO_ID + 1] << 8 | (uint32_t)temp[STS_DIAG_2_ID - IP_TOA_LO_ID]) & 0x3FFFFF; // F1 for STS [21:0]
        diagnostics->stsF2 = ((uint32_t)temp[STS_DIAG_3_ID - IP_TOA_LO_ID + 3] << 24 | (uint32_t)temp[STS_DIAG_3_ID - IP_TOA_LO_ID + 2] << 16
            | (uint32_t)temp[STS_DIAG_3_ID - IP_TOA_LO_ID + 1] << 8 | (uint32_t)temp[STS_DIAG_3_ID - IP_TOA_LO_ID]) & 0x3FFFFF; // F2 for STS [21:0]


        offset_0xd = 0x6c; // there are 0x6C bytes in 0xC0000 base before we enter 0xD0000

        diagnostics->stsF3 = ((uint32_t)temp[STS_DIAG_4_ID - STS_DIAG_4_ID + offset_0xd + 3] << 24 | (uint32_t)temp[STS_DIAG_4_ID - STS_DIAG_4_ID + offset_0xd + 2] << 16
            | (uint32_t)temp[STS_DIAG_4_ID - STS_DIAG_4_ID + offset_0xd + 1] << 8 | (uint32_t)temp[STS_DIAG_4_ID - STS_DIAG_4_ID + offset_0xd]) & 0x3FFFFF; // F3 for STS [21:0]
        diagnostics->stsFpIndex = ((uint16_t)temp[STS_DIAG_8_ID - STS_DIAG_4_ID + offset_0xd + 1] << 8 | temp[STS_DIAG_8_ID - STS_DIAG_4_ID + offset_0xd]) & 0x7FFF;   // First path index [14:0] for STS
        diagnostics->stsAccumCount = ((uint16_t)temp[STS_DIAG_12_ID - STS_DIAG_4_ID + offset_0xd + 1] << 8 | temp[STS_DIAG_12_ID - STS_DIAG_4_ID + offset_0xd]) & 0xFFF;   // Number accumulated symbols [11:0] for STS

        //STS 2
        diagnostics->sts2Peak = ((uint32_t)temp[STS1_DIAG_0_ID - STS_DIAG_4_ID + offset_0xd + 3] << 24 | (uint32_t)temp[STS1_DIAG_0_ID - STS_DIAG_4_ID + offset_0xd + 2] << 16
            | (uint32_t)temp[STS1_DIAG_0_ID - STS_DIAG_4_ID + offset_0xd + 1] << 8 | (uint32_t)temp[STS1_DIAG_0_ID - STS_DIAG_4_ID + offset_0xd]) & 0x3FFFFFFF; // index [29:21] and amplitude [20:0] of peak sample in STS CIR
        diagnostics->sts2Power = ((uint16_t)temp[STS1_DIAG_1_ID - STS_DIAG_4_ID + offset_0xd + 1] << 8 | temp[STS1_DIAG_1_ID - STS_DIAG_4_ID + offset_0xd]);           // channel area allows estimation of channel power for the STS
        diagnostics->sts2F1 = ((uint32_t)temp[STS1_DIAG_2_ID - STS_DIAG_4_ID + offset_0xd + 3] << 24 | (uint32_t)temp[STS1_DIAG_2_ID - STS_DIAG_4_ID + offset_0xd + 2] << 16
            | (uint32_t)temp[STS1_DIAG_2_ID - STS_DIAG_4_ID + offset_0xd + 1] << 8 | (uint32_t)temp[STS1_DIAG_2_ID - STS_DIAG_4_ID + offset_0xd]) & 0x3FFFFF; // F1 for STS [21:0]
        diagnostics->sts2F2 = ((uint32_t)temp[STS1_DIAG_3_ID - STS_DIAG_4_ID + offset_0xd + 3] << 24 | (uint32_t)temp[STS1_DIAG_3_ID - STS_DIAG_4_ID + offset_0xd + 2] << 16
            | (uint32_t)temp[STS1_DIAG_3_ID - STS_DIAG_4_ID + offset_0xd + 1] << 8 | (uint32_t)temp[STS1_DIAG_3_ID - STS_DIAG_4_ID + offset_0xd]) & 0x3FFFFF; // F2 for STS [21:0]
        diagnostics->sts2F3 = ((uint32_t)temp[STS1_DIAG_4_ID - STS_DIAG_4_ID + offset_0xd + 3] << 24 | (uint32_t)temp[STS1_DIAG_4_ID - STS_DIAG_4_ID + offset_0xd + 2] << 16
            | (uint32_t)temp[STS1_DIAG_4_ID - STS_DIAG_4_ID + offset_0xd + 1] << 8 | (uint32_t)temp[STS1_DIAG_4_ID - STS_DIAG_4_ID + offset_0xd]) & 0x3FFFFF; // F3 for STS [21:0]
        diagnostics->sts2FpIndex = ((uint16_t)temp[STS1_DIAG_8_ID - STS_DIAG_4_ID + offset_0xd + 1] << 8 | temp[STS1_DIAG_8_ID - STS_DIAG_4_ID + offset_0xd]) & 0x7FFF;   // First path index [14:0] for STS
        diagnostics->sts2AccumCount = ((uint16_t)temp[STS1_DIAG_12_ID - STS_DIAG_4_ID + offset_0xd + 1] << 8 | temp[STS1_DIAG_12_ID - STS_DIAG_4_ID + offset_0xd]) & 0xFFF;   // Number accumulated symbols [11:0] for STS
        break;
    }
}

/*! ------------------------------------------------------------------------------------------------------------------
 * @brief This is used to read the TX timestamp (adjusted with the programmed antenna delay)
 *
 * input parameters
 * @param timestamp - a pointer to a 5-byte buffer which will store the read TX timestamp time
 *
 * output parameters - the timestamp buffer will contain the value after the function call
 *
 * no return value
 */
void dwt_readtxtimestamp(uint8_t * timestamp)
{
    dwt_readfromdevice(TX_TIME_LO_ID, 0, TX_TIME_TX_STAMP_LEN, timestamp); // Read bytes directly into buffer
}

/*! ------------------------------------------------------------------------------------------------------------------
 * @brief This is used to read the high 32-bits of the TX timestamp (adjusted with the programmed antenna delay)
 *
 * input parameters
 *
 * output parameters
 *
 * returns high 32-bits of TX timestamp
 */
uint32_t dwt_readtxtimestamphi32(void)
{
    return dwt_read32bitoffsetreg(TX_TIME_LO_ID, 1); // Offset is 1 to get the 4 upper bytes out of 5
}

/*! ------------------------------------------------------------------------------------------------------------------
 * @brief This is used to read the low 32-bits of the TX timestamp (adjusted with the programmed antenna delay)
 *
 * input parameters
 *
 * output parameters
 *
 * returns low 32-bits of TX timestamp
 */
uint32_t dwt_readtxtimestamplo32(void)
{
    return dwt_read32bitreg(TX_TIME_LO_ID); // Read TX TIME as a 32-bit register to get the 4 lower bytes out of 5
}

/*! ------------------------------------------------------------------------------------------------------------------
* @brief This is used to read the PDOA result, it is the phase difference between either the Ipatov and STS POA (in PDOA mode 1),
*  or the two STS POAs (in PDOA mode 3), depending on the PDOA mode of operation. (POA - Phase Of Arrival)
*
* NOTE: To convert to degrees: float pdoa_deg = ((float)pdoa / (1 << 11)) * 180 / M_PI
*
* input parameters
*
* output parameters - the PDOA result (signed in [1:-11] radian units)
*
* no return value
*/
int16_t dwt_readpdoa(void)
{
    int16_t  pdoa;

    switch (pdw3000local->dblbuffon)    //check if in double buffer mode and if so which buffer host is currently accessing
    {
    case DBL_BUFF_ACCESS_BUFFER_1:
        //!!! Assumes that Indirect pointer register B was already set. This is done in the dwt_setdblrxbuffmode when mode is enabled.
        pdoa = dwt_read16bitoffsetreg(INDIRECT_POINTER_B_ID, BUF1_PDOA-BUF1_RX_FINFO+2) & (CIA_TDOA_1_PDOA_PDOA_BIT_MASK>>16);
        break;
    case DBL_BUFF_ACCESS_BUFFER_0:
        pdoa = dwt_read16bitoffsetreg(BUF0_PDOA, 2) & (CIA_TDOA_1_PDOA_PDOA_BIT_MASK>>16);
        break;
    default:
        pdoa = dwt_read16bitoffsetreg(CIA_TDOA_1_PDOA_ID, 2) & (CIA_TDOA_1_PDOA_PDOA_BIT_MASK>>16); // phase difference of the 2 POAs
        break;
    }

    if (pdoa & B12_SIGN_EXTEND_TEST) pdoa |= B12_SIGN_EXTEND_MASK; //sign extend
    return pdoa;
}

/*! ------------------------------------------------------------------------------------------------------------------
 * @brief This function is used to read the TDOA (Time Difference On Arrival). The TDOA value that is read from the
 * register is 41-bits in length. However, 6 bytes (or 48 bits) are read from the register. The remaining 7 bits at
 * the 'top' of the 6 bytes that are not part of the TDOA value should be set to zero and should not interfere with
 * rest of the 41-bit value. However, there is no harm in masking the returned value.
 *
 * input parameters
 *
 * output parameters
 * @param tdoa: time difference on arrival - buffer of 6 bytes that will be filled with TDOA value by calling this function
 *
 * no return value
 */
void dwt_readtdoa(uint8_t * tdoa)
{
    // timestamp difference of the 2 cipher RX timestamps
    dwt_readfromdevice(CIA_TDOA_0_ID, 0, CIA_TDOA_LEN, tdoa);
    tdoa[5] &= 0x01; // TDOA value is 41 bits long. You will need to read 6 bytes and mask the highest byte with 0x01
}

/*! ------------------------------------------------------------------------------------------------------------------
 * @brief This is used to read the RX timestamp (adjusted time of arrival)
 *
 * input parameters
 * @param timestamp - a pointer to a 5-byte buffer which will store the read RX timestamp time
 *
 * output parameters - the timestamp buffer will contain the value after the function call
 *
 * no return value
 */
void dwt_readrxtimestamp(uint8_t * timestamp)
{
    switch (pdw3000local->dblbuffon)    //check if in double buffer mode and if so which buffer host is currently accessing
    {
    case DBL_BUFF_ACCESS_BUFFER_1:
        //!!! Assumes that Indirect pointer register B was already set. This is done in the dwt_setdblrxbuffmode when mode is enabled.
        dwt_readfromdevice(INDIRECT_POINTER_B_ID, BUF1_RX_TIME -BUF1_RX_FINFO, RX_TIME_RX_STAMP_LEN, timestamp);
        break;
    case DBL_BUFF_ACCESS_BUFFER_0:
        dwt_readfromdevice(BUF0_RX_TIME, 0, RX_TIME_RX_STAMP_LEN, timestamp);
        break;
    default:
        dwt_readfromdevice(RX_TIME_0_ID, 0, RX_TIME_RX_STAMP_LEN, timestamp); // Get the adjusted time of arrival
        break;
    }
}

/*! ------------------------------------------------------------------------------------------------------------------
 * @brief This is used to read the raw RX timestamp (RMARKER time) before any CIA first path analysis adjustments
 *
 * input parameters
 * @param timestamp - a pointer to a 4-byte buffer which will store the read RX timestamp time
 *
 * output parameters - the timestamp buffer will contain the value after the function call
 *
 * no return value
 */
void dwt_readrxtimestampunadj(uint8_t * timestamp)
{
    timestamp[0] = 0;
    dwt_readfromdevice(RX_TIME_RAW_ID, 0, RX_TIME_RX_STAMP_LEN-1, &timestamp[1]);
}

/*! ------------------------------------------------------------------------------------------------------------------
 * @brief This is used to read the RX timestamp (adjusted time of arrival) w.r.t. Ipatov CIR
 *
 * input parameters
 * @param timestamp - a pointer to a 5-byte buffer which will store the read RX timestamp time
 *
 * output parameters - the timestamp buffer will contain the value after the function call
 *
 * no return value
 */
void dwt_readrxtimestamp_ipatov(uint8_t * timestamp)
{
    switch (pdw3000local->dblbuffon)    //check if in double buffer mode and if so which buffer host is currently accessing
    {
    case DBL_BUFF_ACCESS_BUFFER_1:
        //!!! Assumes that Indirect pointer register B was already set. This is done in the dwt_setdblrxbuffmode when mode is enabled.
        dwt_readfromdevice(INDIRECT_POINTER_B_ID, BUF1_IP_TS - BUF1_RX_FINFO, CIA_I_RX_TIME_LEN, timestamp);
        break;
    case DBL_BUFF_ACCESS_BUFFER_0:
        dwt_readfromdevice(BUF0_IP_TS, 0, CIA_I_RX_TIME_LEN, timestamp);
        break;
    default:
        dwt_readfromdevice(IP_TOA_LO_ID, 0, CIA_I_RX_TIME_LEN, timestamp); // Get the adjusted time of arrival w.r.t. Ipatov CIR
        break;
    }
}

/*! ------------------------------------------------------------------------------------------------------------------
 * @brief This is used to read the RX timestamp (adjusted time of arrival) w.r.t. STS CIR
 *
 * input parameters
 * @param timestamp - a pointer to a 5-byte buffer which will store the read RX timestamp time
 *
 * output parameters - the timestamp buffer will contain the value after the function call
 *
 * no return value
 */
void dwt_readrxtimestamp_sts(uint8_t * timestamp)
{
    switch (pdw3000local->dblbuffon)    //check if in double buffer mode and if so which buffer host is currently accessing
    {
    case DBL_BUFF_ACCESS_BUFFER_1:
        //!!! Assumes that Indirect pointer register B was already set. This is done in the dwt_setdblrxbuffmode when mode is enabled.
        dwt_readfromdevice(INDIRECT_POINTER_B_ID, BUF1_STS_TS - BUF1_RX_FINFO, CIA_C_RX_TIME_LEN, timestamp);
        break;
    case DBL_BUFF_ACCESS_BUFFER_0:
        dwt_readfromdevice(BUF0_STS_TS, 0, CIA_C_RX_TIME_LEN, timestamp);
        break;
    default:
        dwt_readfromdevice(STS_TOA_LO_ID, 0, CIA_C_RX_TIME_LEN, timestamp); // Get the adjusted time of arrival w.r.t. STS CIR
        break;
    }
}

/*! ------------------------------------------------------------------------------------------------------------------
 * @brief This is used to read the high 32-bits of the RX timestamp (adjusted with the programmed antenna delay)
 *
 * input parameters
 *
 * output parameters
 *
 * returns high 32-bits of RX timestamp
 */
uint32_t dwt_readrxtimestamphi32(void)
{
    return dwt_read32bitoffsetreg(RX_TIME_0_ID, 1); // Offset is 1 to get the 4 upper bytes out of 5 byte tiemstamp
}

/*! ------------------------------------------------------------------------------------------------------------------
 * @brief This is used to read the low 32-bits of the RX timestamp (adjusted with the programmed antenna delay)
 *
 * input parameters
 *
 * output parameters
 *
 * returns low 32-bits of RX timestamp
 */
uint32_t dwt_readrxtimestamplo32(void)
{
    return dwt_read32bitreg(RX_TIME_0_ID); // Read RX TIME as a 32-bit register to get the 4 lower bytes out of 5 byte timestamp
}

/*! ------------------------------------------------------------------------------------------------------------------
 * @brief This is used to read the high 32-bits of the system time
 *
 * input parameters
 *
 * output parameters
 *
 * returns high 32-bits of system time timestamp
 */
uint32_t dwt_readsystimestamphi32(void)
{
    return dwt_read32bitreg(SYS_TIME_ID);
}

/*! ------------------------------------------------------------------------------------------------------------------
 * @brief This is used to read the system time
 *
 * input parameters
 * @param timestamp - a pointer to a 4-byte buffer which will store the read system time
 *
 * output parameters
 * @param timestamp - the timestamp buffer will contain the value after the function call
 *
 * no return value
 */
void dwt_readsystime(uint8_t * timestamp)
{
    dwt_readfromdevice(SYS_TIME_ID, 0, SYS_TIME_LEN, timestamp);
}

/*! ------------------------------------------------------------------------------------------------------------------
 * @brief This is used to enable the frame filtering - (the default option is to
 * accept any data and ACK frames with correct destination address)
 *
 * input parameters
 * @param enabletype (bitmask) - enables/disables the frame filtering and configures 802.15.4 type
 *       DWT_FF_ENABLE_802_15_4      0x2             // use 802.15.4 filtering rules
 *       DWT_FF_DISABLE              0x0             // disable FF
 * @param filtermode (bitmask) - configures the frame filtering options according to
 *       DWT_FF_BEACON_EN            0x001           // beacon frames allowed
 *       DWT_FF_DATA_EN              0x002           // data frames allowed
 *       DWT_FF_ACK_EN               0x004           // ack frames allowed
 *       DWT_FF_MAC_EN               0x008           // mac control frames allowed
 *       DWT_FF_RSVD_EN              0x010           // reserved frame types allowed
 *       DWT_FF_MULTI_EN             0x020           // multipurpose frames allowed
 *       DWT_FF_FRAG_EN              0x040           // fragmented frame types allowed
 *       DWT_FF_EXTEND_EN            0x080           // extended frame types allowed
 *       DWT_FF_COORD_EN             0x100           // behave as coordinator (can receive frames with no dest address (PAN ID has to match))
 *       DWT_FF_IMPBRCAST_EN         0x200           // allow MAC implicit broadcast
 *       DWT_FF_LE0_PEND             0x400           // Data pending for device at LE0 address. see dwt_configure_le_address for more info
 *       DWT_FF_LE1_PEND             0x800           // Data pending for device at LE1 address. see dwt_configure_le_address for more info
 *       DWT_FF_LE2_PEND             0x1000           // Data pending for device at LE2 address. see dwt_configure_le_address for more info
 *       DWT_FF_LE3_PEND             0x2000          // Data pending for device at LE3 address. see dwt_configure_le_address for more info
 *       DWT_SSADRAPE                0x4000          //Short Source Address Data Request ACK with PEND Enable
 *       DWT_LSADRAPE                0x8000          //Long Source Address Data Request ACK with PEND Enable
 * output parameters
 *
 * no return value
 */
void dwt_configureframefilter(uint16_t enabletype, uint16_t filtermode)
{
    if(enabletype == DWT_FF_ENABLE_802_15_4)
    {
        dwt_or8bitoffsetreg(SYS_CFG_ID, 0, (uint8_t)(SYS_CFG_FFEN_BIT_MASK));
        dwt_write16bitoffsetreg(ADR_FILT_CFG_ID, 0, filtermode);
    }
    else
    {
        // Disable frame filter
        dwt_and8bitoffsetreg(SYS_CFG_ID, 0, (uint8_t)(~(SYS_CFG_FFEN_BIT_MASK)));
        // Clear the configuration
        dwt_write16bitoffsetreg(ADR_FILT_CFG_ID, 0, 0x0);
    }
}

/*! ------------------------------------------------------------------------------------------------------------------
 * @brief This is used to set the PAN ID
 *
 * input parameters
 * @param panID - this is the PAN ID
 *
 * output parameters
 *
 * no return value
 */
void dwt_setpanid(uint16_t panID)
{
    // PAN ID is high 16 bits of register
    dwt_write16bitoffsetreg(PANADR_ID, PANADR_PAN_ID_BYTE_OFFSET, panID);
}

/*! ------------------------------------------------------------------------------------------------------------------
 * @brief This is used to set 16-bit (short) address
 *
 * input parameters
 * @param shortAddress - this sets the 16 bit short address
 *
 * output parameters
 *
 * no return value
 */
void dwt_setaddress16(uint16_t shortAddress)
{
    // Short address into low 16 bits
    dwt_write16bitoffsetreg(PANADR_ID, PANADR_SHORTADDR_BIT_OFFSET, shortAddress);
}

/*! ------------------------------------------------------------------------------------------------------------------
 * @brief This is used to set the EUI 64-bit (long) address
 *
 * input parameters
 * @param eui64 - this is the pointer to a buffer that contains the 64bit address
 *
 * output parameters
 *
 * no return value
 */
void dwt_seteui(uint8_t *eui64)
{
    dwt_writetodevice(EUI_64_LO_ID, 0, 0x8, eui64);
}

/*! ------------------------------------------------------------------------------------------------------------------
 * @brief This is used to get the EUI 64-bit from the DW3000
 *
 * input parameters
 * @param eui64 - this is the pointer to a buffer that will contain the read 64-bit EUI value
 *
 * output parameters
 *
 * no return value
 */
void dwt_geteui(uint8_t *eui64)
{
    dwt_readfromdevice(EUI_64_LO_ID, 0, 0x8, eui64);
}

/*! ------------------------------------------------------------------------------------------------------------------
* @brief This is used to read from AON memory
*
* input parameters
* @param aon_address - this is the address of the memory location to read
*
* output parameters - None
*
* returns 8-bits read from given AON memory address
*/
uint8_t dwt_aon_read(uint16_t aon_address)
{
    dwt_write16bitoffsetreg(AON_ADDR_ID, 0x0, aon_address);// Set short AON address for read
    dwt_write8bitoffsetreg(AON_CTRL_ID, 0x0, (AON_CTRL_DCA_ENAB_BIT_MASK | AON_CTRL_DCA_READ_EN_BIT_MASK));
    dwt_write8bitoffsetreg(AON_CTRL_ID, 0x0, 0x0);// Clear all enabled bits
    return dwt_read8bitoffsetreg(AON_RDATA_ID, 0x0);//Return the data that was read
}

/*! ------------------------------------------------------------------------------------------------------------------
* @brief This is used to write to AON memory
*
* @param aon_address - this is the address of the memory location to write
* @param aon_write_data - this is the data to write
*
* output parameters - None
*
* no return value
*
*/
void dwt_aon_write(uint16_t aon_address, uint8_t aon_write_data)
{
    uint8_t temp = 0;
    if (aon_address >= 0x100) temp = AON_CTRL_DCA_WRITE_HI_EN_BIT_MASK;
    dwt_write16bitoffsetreg(AON_ADDR_ID, 0x0, aon_address); // Set AON address for write
    dwt_write8bitoffsetreg(AON_WDATA_ID, 0x0, aon_write_data); // Set write data
    dwt_write8bitoffsetreg(AON_CTRL_ID,0x0,(temp | AON_CTRL_DCA_ENAB_BIT_MASK | AON_CTRL_DCA_WRITE_EN_BIT_MASK ));//Enable write
    dwt_write8bitoffsetreg(AON_CTRL_ID, 0x0, 0x0); // Clear all enabled bits
}

/*! ------------------------------------------------------------------------------------------------------------------
 * @brief This is used to read the OTP data from given address into provided array
 *
 * input parameters
 * @param address - this is the OTP address to read from
 * @param array - this is the pointer to the array into which to read the data
 * @param length - this is the number of 32 bit words to read (array needs to be at least this length)
 *
 * output parameters
 *
 * no return value
 */
void dwt_otpread(uint16_t address, uint32_t *array, uint8_t length)
{
    int i;

    for(i=0; i<length; i++)
    {
        array[i] = _dwt_otpread(address + i);
    }

    return ;
}

/*! ------------------------------------------------------------------------------------------------------------------
 * @brief function to read the OTP memory.
 *
 * input parameters
 * @param address - address to read at
 *
 * output parameters
 *
 * returns the 32bit of read data
 */
uint32_t _dwt_otpread(uint16_t address)
{
    uint32_t ret_data = 0;

    // Set manual access mode
    dwt_write16bitoffsetreg(OTP_CFG_ID, 0, 0x0001);
    // set the address
    dwt_write16bitoffsetreg(OTP_ADDR_ID, 0, address);
    // Assert the read strobe
    dwt_write16bitoffsetreg(OTP_CFG_ID, 0, 0x0002);
    // attempt a read from OTP address
    ret_data = dwt_read32bitoffsetreg(OTP_RDATA_ID, 0);

    // Return the 32bit of read data
    return ret_data;
}

/*! ------------------------------------------------------------------------------------------------------------------
 * @brief For each value to send to OTP bloc, following two register writes are required as shown below
 *
 * @param val: 16-bit value to write to the OTP block
 */
void  __dwt_otp_write_wdata_id_reg(int16_t val)
{
    /* Pull the CS high to enable user interface for programming */
	/* 'val' is ignored in this instance by the OTP block */
	dwt_write16bitoffsetreg(OTP_WDATA_ID, 0, 0x0200 | val);
	/* Send the relevant command to the OTP block */
    dwt_write16bitoffsetreg(OTP_WDATA_ID, 0, 0x0000 | val);
}
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
