asinghani/drive-by-wireless/firmware/utils.c

#include <stdio.h>
#include "pico/stdio.h"
#include "pico/stdlib.h"
#include "utils.h"

void _xassert_fail(const char* cond, int line) {
    while (1) {
        printf("Assertion '%s' failed on line %d. Please add more magic.\n",
                cond, line);
        busy_wait_ms(2000);
    }
}

int clamp(int x, int lo, int hi) {
    if (x > hi) return hi;
    if (x < lo) return lo;
    return x;
}

float absf(float x) {
    if (x < 0) return -x;
    return x;
}

int32_t millis() {
    absolute_time_t ts = get_absolute_time();
    return to_ms_since_boot(ts);
}
